kalebwbishop/smart-handicap-sign/frontend/pnpm-lock.yaml

lockfileVersion: '9.0'

settings:
  autoInstallPeers: true
  excludeLinksFromLockfile: false

importers:

  .:
    devDependencies:
      turbo:
        specifier: ^2.1.3
        version: 2.9.16
      typescript:
        specifier: ^5.6.3
        version: 5.9.3

  apps/mobile:
    dependencies:
      '@expo-google-fonts/jetbrains-mono':
        specifier: ^0.4.1
        version: 0.4.1
      '@expo-google-fonts/montserrat':
        specifier: ^0.4.2
        version: 0.4.2
      '@expo-google-fonts/outfit':
        specifier: ^0.4.3
        version: 0.4.3
      '@expo/metro-runtime':
        specifier: ~6.1.2
        version: 6.1.2(expo@54.0.35)(react-dom@19.1.0(react@19.1.0))(react-native@0.81.5(@babel/core@7.29.7)(@react-native/metro-config@0.85.3(@babel/core@7.29.7))(@types/react@19.1.17)(react@19.1.0))(react@19.1.0)
      '@expo/vector-icons':
        specifier: ^15.0.3
        version: 15.1.1(expo-font@14.0.12)(react-native@0.81.5(@babel/core@7.29.7)(@react-native/metro-config@0.85.3(@babel/core@7.29.7))(@types/react@19.1.17)(react@19.1.0))(react@19.1.0)
      '@hazard-hero/shared':
        specifier: workspace:*
        version: link:../../packages/shared
      '@react-native-async-storage/async-storage':
        specifier: 2.2.0
        version: 2.2.0(react-native@0.81.5(@babel/core@7.29.7)(@react-native/metro-config@0.85.3(@babel/core@7.29.7))(@types/react@19.1.17)(react@19.1.0))
      '@react-navigation/native':
        specifier: ^6.1.9
        version: 6.1.18(react-native@0.81.5(@babel/core@7.29.7)(@react-native/metro-config@0.85.3(@babel/core@7.29.7))(@types/react@19.1.17)(react@19.1.0))(react@19.1.0)
      '@react-navigation/native-stack':
        specifier: ^6.9.17
        version: 6.11.0(@react-navigation/native@6.1.18(react-native@0.81.5(@babel/core@7.29.7)(@react-native/metro-config@0.85.3(@babel/core@7.29.7))(@types/react@19.1.17)(react@19.1.0))(react@19.1.0))(react-native-safe-area-context@5.6.2(react-native@0.81.5(@babel/core@7.29.7)(@react-native/metro-config@0.85.3(@babel/core@7.29.7))(@types/react@19.1.17)(react@19.1.0))(react@19.1.0))(react-native-screens@4.16.0(react-native@0.81.5(@babel/core@7.29.7)(@react-native/metro-config@0.85.3(@babel/core@7.29.7))(@types/react@19.1.17)(react@19.1.0))(react@19.1.0))(react-native@0.81.5(@babel/core@7.29.7)(@react-native/metro-config@0.85.3(@babel/core@7.29.7))(@types/react@19.1.17)(react@19.1.0))(react@19.1.0)
      '@tanstack/react-query':
        specifier: ^5.17.9
        version: 5.101.0(react@19.1.0)
      axios:
        specifier: ^1.9.0
        version: 1.17.0
      deploy-box-react-native:
        specifier: file:../../../../deploy-box-react-native
        version: file:../../deploy-box-react-native(axios@1.17.0)(expo-linking@8.0.12)(expo-router@56.2.9)(expo-secure-store@15.0.8(expo@54.0.35))(expo-web-browser@55.0.16(expo@54.0.35)(react-native@0.81.5(@babel/core@7.29.7)(@react-native/metro-config@0.85.3(@babel/core@7.29.7))(@types/react@19.1.17)(react@19.1.0)))(react-native@0.81.5(@babel/core@7.29.7)(@react-native/metro-config@0.85.3(@babel/core@7.29.7))(@types/react@19.1.17)(react@19.1.0))(react@19.1.0)(zustand@4.5.7(@types/react@19.1.17)(react@19.1.0))
      expo:
        specifier: ~54.0.32
        version: 54.0.35(@babel/core@7.29.7)(@expo/dom-webview@56.0.5)(@expo/metro-runtime@6.1.2)(expo-router@56.2.9)(react-native@0.81.5(@babel/core@7.29.7)(@react-native/metro-config@0.85.3(@babel/core@7.29.7))(@types/react@19.1.17)(react@19.1.0))(react@19.1.0)(typescript@5.9.3)
      expo-av:
        specifier: ~16.0.8
        version: 16.0.8(expo@54.0.35)(react-native-web@0.21.2(react-dom@19.1.0(react@19.1.0))(react@19.1.0))(react-native@0.81.5(@babel/core@7.29.7)(@react-native/metro-config@0.85.3(@babel/core@7.29.7))(@types/react@19.1.17)(react@19.1.0))(react@19.1.0)
      expo-constants:
        specifier: ~18.0.10
        version: 18.0.13(expo@54.0.35)(react-native@0.81.5(@babel/core@7.29.7)(@react-native/metro-config@0.85.3(@babel/core@7.29.7))(@types/react@19.1.17)(react@19.1.0))
      expo-crypto:
        specifier: ~15.0.2
        version: 15.0.9(expo@54.0.35)
      expo-device:
        specifier: ~8.0.9
        version: 8.0.10(expo@54.0.35)
      expo-font:
        specifier: ~14.0.10
        version: 14.0.12(expo@54.0.35)(react-native@0.81.5(@babel/core@7.29.7)(@react-native/metro-config@0.85.3(@babel/core@7.29.7))(@types/react@19.1.17)(react@19.1.0))(react@19.1.0)
      expo-linking:
        specifier: ~8.0.11
        version: 8.0.12(expo@54.0.35)(react-native@0.81.5(@babel/core@7.29.7)(@react-native/metro-config@0.85.3(@babel/core@7.29.7))(@types/react@19.1.17)(react@19.1.0))(react@19.1.0)
      expo-notifications:
        specifier: ~0.32.12
        version: 0.32.17(expo@54.0.35)(react-native@0.81.5(@babel/core@7.29.7)(@react-native/metro-config@0.85.3(@babel/core@7.29.7))(@types/react@19.1.17)(react@19.1.0))(react@19.1.0)(typescript@5.9.3)
      expo-secure-store:
        specifier: ~15.0.8
        version: 15.0.8(expo@54.0.35)
      expo-status-bar:
        specifier: ~3.0.9
        version: 3.0.9(react-native@0.81.5(@babel/core@7.29.7)(@react-native/metro-config@0.85.3(@babel/core@7.29.7))(@types/react@19.1.17)(react@19.1.0))(react@19.1.0)
      expo-web-browser:
        specifier: ^55.0.9
        version: 55.0.16(expo@54.0.35)(react-native@0.81.5(@babel/core@7.29.7)(@react-native/metro-config@0.85.3(@babel/core@7.29.7))(@types/react@19.1.17)(react@19.1.0))
      linking:
        specifier: ^0.1.0-beta.5
        version: 0.1.0-beta.5
      react:
        specifier: 19.1.0
        version: 19.1.0
      react-dom:
        specifier: 19.1.0
        version: 19.1.0(react@19.1.0)
      react-native:
        specifier: 0.81.5
        version: 0.81.5(@babel/core@7.29.7)(@react-native/metro-config@0.85.3(@babel/core@7.29.7))(@types/react@19.1.17)(react@19.1.0)
      react-native-safe-area-context:
        specifier: ~5.6.0
        version: 5.6.2(react-native@0.81.5(@babel/core@7.29.7)(@react-native/metro-config@0.85.3(@babel/core@7.29.7))(@types/react@19.1.17)(react@19.1.0))(react@19.1.0)
      react-native-screens:
        specifier: ~4.16.0
        version: 4.16.0(react-native@0.81.5(@babel/core@7.29.7)(@react-native/metro-config@0.85.3(@babel/core@7.29.7))(@types/react@19.1.17)(react@19.1.0))(react@19.1.0)
      react-native-sse:
        specifier: ^1.2.1
        version: 1.2.1
      react-native-svg:
        specifier: ^15.15.5
        version: 15.15.5(react-native@0.81.5(@babel/core@7.29.7)(@react-native/metro-config@0.85.3(@babel/core@7.29.7))(@types/react@19.1.17)(react@19.1.0))(react@19.1.0)
      react-native-web:
        specifier: ^0.21.0
        version: 0.21.2(react-dom@19.1.0(react@19.1.0))(react@19.1.0)
      react-secure-storage:
        specifier: ^1.3.2
        version: 1.3.2
      zustand:
        specifier: ^4.4.7
        version: 4.5.7(@types/react@19.1.17)(react@19.1.0)
    devDependencies:
      '@babel/core':
        specifier: ^7.23.7
        version: 7.29.7
      '@playwright/test':
        specifier: ^1.59.1
        version: 1.60.0
      '@testing-library/react-native':
        specifier: ^12.4.3
        version: 12.9.0(jest@29.7.0(@types/node@22.19.20))(react-native@0.81.5(@babel/core@7.29.7)(@react-native/metro-config@0.85.3(@babel/core@7.29.7))(@types/react@19.1.17)(react@19.1.0))(react-test-renderer@19.1.0(react@19.1.0))(react@19.1.0)
      '@types/react':
        specifier: ~19.1.10
        version: 19.1.17
      '@types/react-native':
        specifier: ~0.73.0
        version: 0.73.0(@babel/core@7.29.7)(@react-native/metro-config@0.85.3(@babel/core@7.29.7))(@types/react@19.1.17)(react@19.1.0)
      '@types/react-navigation':
        specifier: ^3.0.8
        version: 3.4.0
      '@typescript-eslint/eslint-plugin':
        specifier: ^8.60.0
        version: 8.60.1(@typescript-eslint/parser@8.60.1(eslint@8.57.1)(typescript@5.9.3))(eslint@8.57.1)(typescript@5.9.3)
      '@typescript-eslint/parser':
        specifier: ^8.60.0
        version: 8.60.1(eslint@8.57.1)(typescript@5.9.3)
      eslint:
        specifier: ^8.56.0
        version: 8.57.1
      eslint-config-expo:
        specifier: ~10.0.0
        version: 10.0.0(eslint@8.57.1)(typescript@5.9.3)
      jest:
        specifier: ^29.7.0
        version: 29.7.0(@types/node@22.19.20)
      playwright:
        specifier: ^1.59.1
        version: 1.60.0
      react-native-dotenv:
        specifier: ^3.4.11
        version: 3.4.11(@babel/runtime@7.29.7)
      react-test-renderer:
        specifier: 19.1.0
        version: 19.1.0(react@19.1.0)
      typescript:
        specifier: ^5.3.3
        version: 5.9.3

  apps/web:
    dependencies:
      '@hazard-hero/shared':
        specifier: workspace:*
        version: link:../../packages/shared
      axios:
        specifier: ^1.9.0
        version: 1.17.0
      next:
        specifier: ^15.4.0
        version: 15.5.19(@playwright/test@1.60.0)(babel-plugin-react-compiler@1.0.0)(react-dom@19.1.0(react@19.1.0))(react@19.1.0)
      react:
        specifier: 19.1.0
        version: 19.1.0
      react-dom:
        specifier: 19.1.0
        version: 19.1.0(react@19.1.0)
    devDependencies:
      '@types/node':
        specifier: ^22.10.2
        version: 22.19.20
      '@types/react':
        specifier: ^19.1.10
        version: 19.1.17
      '@types/react-dom':
        specifier: ^19.1.9
        version: 19.2.3(@types/react@19.1.17)
      typescript:
        specifier: ^5.6.3
        version: 5.9.3

  packages/eslint-config: {}

  packages/shared:
    devDependencies:
      typescript:
        specifier: ^5.6.3
        version: 5.9.3

  packages/tsconfig: {}

  packages/ui:
    devDependencies:
      typescript:
        specifier: ^5.6.3
        version: 5.9.3

packages:

  '@0no-co/graphql.web@1.2.0':
    resolution: {integrity: sha512-/1iHy9TTr63gE1YcR5idjx8UREz1s0kFhydf3bBLCXyqjhkIc6igAzTOx3zPifCwFR87tsh/4Pa9cNts6d2otw==}
    peerDependencies:
      graphql: ^14.0.0 || ^15.0.0 || ^16.0.0
    peerDependenciesMeta:
      graphql:
        optional: true

  '@adobe/css-tools@4.5.0':
    resolution: {integrity: sha512-6OzddxPio9UiWTCemp4N8cYLV2ZN1ncRnV1cVGtve7dhPOtRkleRyx32GQCYSwDYgaHU3USMm84tNsvKzRCa1Q==}

  '@babel/code-frame@7.10.4':
    resolution: {integrity: sha512-vG6SvB6oYEhvgisZNFRmRCUkLz11c7rp+tbNTynGqc6mS1d5ATd/sGyV6W0KZZnXRKMTzZDRgQT3Ou9jhpAfUg==}

  '@babel/code-frame@7.29.7':
    resolution: {integrity: sha512-Aup7aUOfpbAUg2ROOJN6Iw5f9DMBlzu0mIkm/malLQFN/YQgO48wCj0Kxa3sEHJvPVFg7siR+qRInwXd2qhQKw==}
    engines: {node: '>=6.9.0'}

  '@babel/compat-data@7.29.7':
    resolution: {integrity: sha512-locTkQyKvwIEgBzVrn8693ebc97F2U8ZHjbXwDXJ5Fn2TCpNwTlKcaKLkdHop5c/icOFE7qt7Q9JC5hnKNa6Gg==}
    engines: {node: '>=6.9.0'}

  '@babel/core@7.29.7':
    resolution: {integrity: sha512-RgHBCvtjbOK2gXSNBNIkNoEc9qoVEtau3hj8gEqKQuL3HZAibKarWFEI3Lfm6EYKkLalOh8eSrj9b+ch9H/VBA==}
    engines: {node: '>=6.9.0'}

  '@babel/generator@7.29.7':
    resolution: {integrity: sha512-DkXD5OJQaAQIdZ1bt3UZdEnHAn9Imd3IVBdX03UFe+ony9Ojw5pzr9YVKGDY1jt+Gcn/FnGkNf8r+Vj5NOJWtQ==}
    engines: {node: '>=6.9.0'}

  '@babel/helper-annotate-as-pure@7.29.7':
    resolution: {integrity: sha512-OoK6239jHPuSQOoS0kfTVKn0b/rVTk0seKq4Gd2UMLtmOVLjDC0ki3e+c90Trqv2gMfvJFqkiljrr568+qddiw==}
    engines: {node: '>=6.9.0'}

  '@babel/helper-compilation-targets@7.29.7':
    resolution: {integrity: sha512-wem6WaBj4NaVYVdNhLPPVacES6ZJ+KBBfSkTMD3YZxbP3rm3Di85tJU5ljaUNhaOynt+Aj0xruhYuzQBt8n71g==}
    engines: {node: '>=6.9.0'}

  '@babel/helper-create-class-features-plugin@7.29.7':
    resolution: {integrity: sha512-IY3ZD9Tmooqr3TUhc3DUWxiuo8xx1DWLhd5M7hQ+ZWJamqM2BbalrBJb2MisSLoYorOj75U03qULCxQTY9r3hg==}
    engines: {node: '>=6.9.0'}
    peerDependencies:
      '@babel/core': ^7.0.0

  '@babel/helper-create-regexp-features-plugin@7.29.7':
    resolution: {integrity: sha512-907Uymvqgg1dwUA+7IGwFAOSYzQOuzPXKNJ1yxzwPffzkYFg2q2eHi1fIOs6sXkG9NbIUMunnUlkYsfRFNvomg==}
    engines: {node: '>=6.9.0'}
    peerDependencies:
      '@babel/core': ^7.0.0

  '@babel/helper-define-polyfill-provider@0.6.8':
    resolution: {integrity: sha512-47UwBLPpQi1NoWzLuHNjRoHlYXMwIJoBf7MFou6viC/sIHWYygpvr0B6IAyh5sBdA2nr2LPIRww8lfaUVQINBA==}
    peerDependencies:
      '@babel/core': ^7.4.0 || ^8.0.0-0 <8.0.0

  '@babel/helper-globals@7.29.7':
    resolution: {integrity: sha512-3nQVUAtvkKH9zahfWgw96Jc/uFOmjACE1kQz82E2lqWmHBgjzbNlsC22nuQTfahmWeQtTq5nQ/4Nnd2A1wj4zA==}
    engines: {node: '>=6.9.0'}

  '@babel/helper-member-expression-to-functions@7.29.7':
    resolution: {integrity: sha512-j+7JYmk1JYDtACIGj0QJqqWZjoUpMoEikQGADMaHgCMCSDqd2+P32rfcibUNrGOMWrlzK1WJBdxrB3JJQZwWtg==}
    engines: {node: '>=6.9.0'}

  '@babel/helper-module-imports@7.29.7':
    resolution: {integrity: sha512-ejHwrQQYcm9xnTivShn2IDOlIzInN34AXskvq9QicvCtEzq1Vzclu/tKF8Jq1Cg8JG2GL6/EmjgsCT7lXepE3g==}
    engines: {node: '>=6.9.0'}

  '@babel/helper-module-transforms@7.29.7':
    resolution: {integrity: sha512-UPUVSyXbOh627KiCIGQSgwWzGeBKLkaJ9PJEdrngIwMSzxLR4jS4+f1f1jb7VzBbg8nFLaYotvVPFCTqdrmTAg==}
    engines: {node: '>=6.9.0'}
    peerDependencies:
      '@babel/core': ^7.0.0

  '@babel/helper-optimise-call-expression@7.29.7':
    resolution: {integrity: sha512-+kmGVjcT9RGYzoDwdwEqEvGgKe3BYq+O1iGzjFubaNgZHwYHP6lsF2Yghf4kEuv9BV7tYDZ913aBW9am6YKong==}
    engines: {node: '>=6.9.0'}

  '@babel/helper-plugin-utils@7.29.7':
    resolution: {integrity: sha512-G7sHYigPY17oO5SYWnfD/0MTBwVR781S/JI643e/JhUYgVgWE/61SoW3NH9KWUKyKq5LVh3npif99Wkt6j86Jw==}
    engines: {node: '>=6.9.0'}

  '@babel/helper-remap-async-to-generator@7.29.7':
    resolution: {integrity: sha512-16AMiW26DbXWBbr3B8wNozKM0ydMLB892vaOaJW/fPJdnT8vJk5sdkQcU/isqUxyCE0cEoa8wZOcbgDuC4b6Og==}
    engines: {node: '>=6.9.0'}
    peerDependencies:
      '@babel/core': ^7.0.0

  '@babel/helper-replace-supers@7.29.7':
    resolution: {integrity: sha512-atfGXWSeCiF4DnKZIfmJfQRkSw9b9gNNXR1kqKjbhG4pGYCOnkp8OcTB8E3NXjBu8NpheSnOeNKz8KT7UNFTmQ==}
    engines: {node: '>=6.9.0'}
    peerDependencies:
      '@babel/core': ^7.0.0

  '@babel/helper-skip-transparent-expression-wrappers@7.29.7':
    resolution: {integrity: sha512-brcMGQaVzIeUb+6/bs1Av0f8YuNNjKY2JyvfRCsFuFsdKccEQ5Ges2y74D74NZ1Rz8lKJ9ksJkfqwQFJ/iNEyQ==}
    engines: {node: '>=6.9.0'}

  '@babel/helper-string-parser@7.29.7':
    resolution: {integrity: sha512-Pb5ijPrZ89GDH8223L4UP8i6QApWxs04RbPQJTeWDV0/keR2E36MeKnyr6LYmUUvqRRI+Iv87SuF1W6ErINzYw==}
    engines: {node: '>=6.9.0'}

  '@babel/helper-validator-identifier@7.29.7':
    resolution: {integrity: sha512-qehxGkRj55h/ff8EMaJ+cYhyaKlHIxqYDn682wQD7RNp9UujOQsHog2uS0r2vzr4pW+sXf90NeeayjcNaX3fFg==}
    engines: {node: '>=6.9.0'}

  '@babel/helper-validator-option@7.29.7':
    resolution: {integrity: sha512-N9ZErrD+yW5geCDtBqnOoxmR8+tNKiGuxKlDpuJxfsqpa2dFcexaziGAE/qoHLiDDreVNMupxGmSoNlyvsA3gw==}
    engines: {node: '>=6.9.0'}

  '@babel/helper-wrap-function@7.29.7':
    resolution: {integrity: sha512-iES0Skag9ERIF68aXadpO6dbXa03mNWK3sEqJaMnLNs/eC3l0lkImdfoy6Y09/SfkpawdAB4RjQ7PVA7TcVGdw==}
    engines: {node: '>=6.9.0'}

  '@babel/helpers@7.29.7':
    resolution: {integrity: sha512-1k2lAGRMfHTcwuNYcCNUmaUffmQv8KWMfh2iJUUeRlwlwH4FdNG7mfPI10NPfLHJFThE4Tyr4mv7kTNZOiPuBg==}
    engines: {node: '>=6.9.0'}

  '@babel/highlight@7.25.9':
    resolution: {integrity: sha512-llL88JShoCsth8fF8R4SJnIn+WLvR6ccFxu1H3FlMhDontdcmZWf2HgIZ7AIqV3Xcck1idlohrN4EUBQz6klbw==}
    engines: {node: '>=6.9.0'}

  '@babel/parser@7.29.7':
    resolution: {integrity: sha512-hnORnjP/1P/zFEndoeX+n+t1RwWRJiJpM/jO7FW32Kn9r5+sJB2JWOdYo4L6k78j15eCwY3Gm/7364B1EMwtNg==}
    engines: {node: '>=6.0.0'}
    hasBin: true

  '@babel/plugin-proposal-decorators@7.29.7':
    resolution: {integrity: sha512-EtU0Hi3GvrTqD56xKmZvV/uCXK2ZbwVNPNLAquVItcAZpUhkXwWlo3Fmj0c2LxgSf2I8IDULeAepwNP1OefLXg==}
    engines: {node: '>=6.9.0'}
    peerDependencies:
      '@babel/core': ^7.0.0-0

  '@babel/plugin-proposal-export-default-from@7.29.7':
    resolution: {integrity: sha512-p+G5BNXDcy3bOXplhY4HybQ1GxH3i2Tppmdm/3epyRu2VgJJZuUlZ61MqRTg582Q7ZLBdP7fePYvsumSEkMxcQ==}
    engines: {node: '>=6.9.0'}
    peerDependencies:
      '@babel/core': ^7.0.0-0

  '@babel/plugin-syntax-async-generators@7.8.4':
    resolution: {integrity: sha512-tycmZxkGfZaxhMRbXlPXuVFpdWlXpir2W4AMhSJgRKzk/eDlIXOhb2LHWoLpDF7TEHylV5zNhykX6KAgHJmTNw==}
    peerDependencies:
      '@babel/core': ^7.0.0-0

  '@babel/plugin-syntax-bigint@7.8.3':
    resolution: {integrity: sha512-wnTnFlG+YxQm3vDxpGE57Pj0srRU4sHE/mDkt1qv2YJJSeUAec2ma4WLUnUPeKjyrfntVwe/N6dCXpU+zL3Npg==}
    peerDependencies:
      '@babel/core': ^7.0.0-0

  '@babel/plugin-syntax-class-properties@7.12.13':
    resolution: {integrity: sha512-fm4idjKla0YahUNgFNLCB0qySdsoPiZP3iQE3rky0mBUtMZ23yDJ9SJdg6dXTSDnulOVqiF3Hgr9nbXvXTQZYA==}
    peerDependencies:
      '@babel/core': ^7.0.0-0

  '@babel/plugin-syntax-class-static-block@7.14.5':
    resolution: {integrity: sha512-b+YyPmr6ldyNnM6sqYeMWE+bgJcJpO6yS4QD7ymxgH34GBPNDM/THBh8iunyvKIZztiwLH4CJZ0RxTk9emgpjw==}
    engines: {node: '>=6.9.0'}
    peerDependencies:
      '@babel/core': ^7.0.0-0

  '@babel/plugin-syntax-decorators@7.29.7':
    resolution: {integrity: sha512-9MTTLbF39X6sqM92JPEsoI7++26hjZvzkxKZy64aMhWLH2mPkJ/Q3AV4QLmls3R14FpSpkOwQQfUh962JGQxxg==}
    engines: {node: '>=6.9.0'}
    peerDependencies:
      '@babel/core': ^7.0.0-0

  '@babel/plugin-syntax-dynamic-import@7.8.3':
    resolution: {integrity: sha512-5gdGbFon+PszYzqs83S3E5mpi7/y/8M9eC90MRTZfduQOYW76ig6SOSPNe41IG5LoP3FGBn2N0RjVDSQiS94kQ==}
    peerDependencies:
      '@babel/core': ^7.0.0-0

  '@babel/plugin-syntax-export-default-from@7.29.7':
    resolution: {integrity: sha512-foag0BB37ROhdeIX9O8G0jX7hw0UekJc04cHMrYLOnrErsnBKqJGHJ8eDRpoCFZBvEPPygmmtw4qyU97qa4oOw==}
    engines: {node: '>=6.9.0'}
    peerDependencies:
      '@babel/core': ^7.0.0-0

  '@babel/plugin-syntax-flow@7.29.7':
    resolution: {integrity: sha512-ajMX6QPcyomotqwpzhkYGxcK2i/us0rs1Qo9QvUpa+Fca0FTmqrzKrctoIYLMxcOhGZldGT/BAVkRGTWBiR8gQ==}
    engines: {node: '>=6.9.0'}
    peerDependencies:
      '@babel/core': ^7.0.0-0

  '@babel/plugin-syntax-import-attributes@7.29.7':
    resolution: {integrity: sha512-zGYcYfq/WmZ4V+kBIXQon9dSSc8ircGZqw9ZaNhhGj9nZkeBu1jHLBDQqYYi5WA9uawvA2sIMbry2nCFhf5Djg==}
    engines: {node: '>=6.9.0'}
    peerDependencies:
      '@babel/core': ^7.0.0-0

  '@babel/plugin-syntax-import-meta@7.10.4':
    resolution: {integrity: sha512-Yqfm+XDx0+Prh3VSeEQCPU81yC+JWZ2pDPFSS4ZdpfZhp4MkFMaDC1UqseovEKwSUpnIL7+vK+Clp7bfh0iD7g==}
    peerDependencies:
      '@babel/core': ^7.0.0-0

  '@babel/plugin-syntax-json-strings@7.8.3':
    resolution: {integrity: sha512-lY6kdGpWHvjoe2vk4WrAapEuBR69EMxZl+RoGRhrFGNYVK8mOPAW8VfbT/ZgrFbXlDNiiaxQnAtgVCZ6jv30EA==}
    peerDependencies:
      '@babel/core': ^7.0.0-0

  '@babel/plugin-syntax-jsx@7.29.7':
    resolution: {integrity: sha512-TSu8+mHCoEaaCDEZ0I3+6mvTBYR4PCxQwf2z9/r5Tbztv6NaLR3B9thGTTxX2WGuGHJqRiAbKPeGTJ5XWXVg6A==}
    engines: {node: '>=6.9.0'}
    peerDependencies:
      '@babel/core': ^7.0.0-0

  '@babel/plugin-syntax-logical-assignment-operators@7.10.4':
    resolution: {integrity: sha512-d8waShlpFDinQ5MtvGU9xDAOzKH47+FFoney2baFIoMr952hKOLp1HR7VszoZvOsV/4+RRszNY7D17ba0te0ig==}
    peerDependencies:
      '@babel/core': ^7.0.0-0

  '@babel/plugin-syntax-nullish-coalescing-operator@7.8.3':
    resolution: {integrity: sha512-aSff4zPII1u2QD7y+F8oDsz19ew4IGEJg9SVW+bqwpwtfFleiQDMdzA/R+UlWDzfnHFCxxleFT0PMIrR36XLNQ==}
    peerDependencies:
      '@babel/core': ^7.0.0-0

  '@babel/plugin-syntax-numeric-separator@7.10.4':
    resolution: {integrity: sha512-9H6YdfkcK/uOnY/K7/aA2xpzaAgkQn37yzWUMRK7OaPOqOpGS1+n0H5hxT9AUw9EsSjPW8SVyMJwYRtWs3X3ug==}
    peerDependencies:
      '@babel/core': ^7.0.0-0

  '@babel/plugin-syntax-object-rest-spread@7.8.3':
    resolution: {integrity: sha512-XoqMijGZb9y3y2XskN+P1wUGiVwWZ5JmoDRwx5+3GmEplNyVM2s2Dg8ILFQm8rWM48orGy5YpI5Bl8U1y7ydlA==}
    peerDependencies:
      '@babel/core': ^7.0.0-0

  '@babel/plugin-syntax-optional-catch-binding@7.8.3':
    resolution: {integrity: sha512-6VPD0Pc1lpTqw0aKoeRTMiB+kWhAoT24PA+ksWSBrFtl5SIRVpZlwN3NNPQjehA2E/91FV3RjLWoVTglWcSV3Q==}
    peerDependencies:
      '@babel/core': ^7.0.0-0

  '@babel/plugin-syntax-optional-chaining@7.8.3':
    resolution: {integrity: sha512-KoK9ErH1MBlCPxV0VANkXW2/dw4vlbGDrFgz8bmUsBGYkFRcbRwMh6cIJubdPrkxRwuGdtCk0v/wPTKbQgBjkg==}
    peerDependencies:
      '@babel/core': ^7.0.0-0

  '@babel/plugin-syntax-private-property-in-object@7.14.5':
    resolution: {integrity: sha512-0wVnp9dxJ72ZUJDV27ZfbSj6iHLoytYZmh3rFcxNnvsJF3ktkzLDZPy/mA17HGsaQT3/DQsWYX1f1QGWkCoVUg==}
    engines: {node: '>=6.9.0'}
    peerDependencies:
      '@babel/core': ^7.0.0-0

  '@babel/plugin-syntax-top-level-await@7.14.5':
    resolution: {integrity: sha512-hx++upLv5U1rgYfwe1xBQUhRmU41NEvpUvrp8jkrSCdvGSnM5/qdRMtylJ6PG5OFkBaHkbTAKTnd3/YyESRHFw==}
    engines: {node: '>=6.9.0'}
    peerDependencies:
      '@babel/core': ^7.0.0-0

  '@babel/plugin-syntax-typescript@7.29.7':
    resolution: {integrity: sha512-ngr+82Sh0xMz25TPCZi+nC2iTzjfCdWS2ONXTp/PtSCHCgaCNBpdMqgvJ2ccdLlClVZ7sisIgB914j/JFe+RZA==}
    engines: {node: '>=6.9.0'}
    peerDependencies:
      '@babel/core': ^7.0.0-0

  '@babel/plugin-transform-arrow-functions@7.29.7':
    resolution: {integrity: sha512-N7zArUXWzAMzm+/N0uPBeVB3Fam5lMxtUwMmDK5f/IBBS7a7p1qeUoxd/6CckXoxUdgsntq1Dh8xNW06maZbDQ==}
    engines: {node: '>=6.9.0'}
    peerDependencies:
      '@babel/core': ^7.0.0-0

  '@babel/plugin-transform-async-generator-functions@7.29.7':
    resolution: {integrity: sha512-d98gXZkgswvkyohMBABkhm3GeXhYj8psWfwQ2C7gtfrKGTykQa/iOIi+JJhwMjPlZ6Vm2XN+DCf3Es1EoG4ZLA==}
    engines: {node: '>=6.9.0'}
    peerDependencies:
      '@babel/core': ^7.0.0-0

  '@babel/plugin-transform-async-to-generator@7.29.7':
    resolution: {integrity: sha512-pcUb2SS+RMo9TWVBwKGI5ShtoG7R+zBsFmCKDa6fe8c+hPr3XJlZgoE5j6i8W7gDjhyvy+85vmYexanvXh3d1w==}
    engines: {node: '>=6.9.0'}
    peerDependencies:
      '@babel/core': ^7.0.0-0

  '@babel/plugin-transform-block-scoping@7.29.7':
    resolution: {integrity: sha512-ONyr4+AZhKh8yKWInVxU9AXA9EbsyeLcL6V0dJy6M2/62vuvpGm29zzuymbTpdc451GEpDIdAyPLP3r+P61yKQ==}
    engines: {node: '>=6.9.0'}
    peerDependencies:
      '@babel/core': ^7.0.0-0

  '@babel/plugin-transform-class-properties@7.29.7':
    resolution: {integrity: sha512-GtcpjFvanPfzNQi3eTitsCqtRRmmqzpy/A+yhTR1HaZo1Ly3EA8ZXxlPyHdR8/IuRMYc3E4wdGBewB2QKQjAaA==}
    engines: {node: '>=6.9.0'}
    peerDependencies:
      '@babel/core': ^7.0.0-0

  '@babel/plugin-transform-class-static-block@7.29.7':
    resolution: {integrity: sha512-kibJgmEdX2iMwsHY2tSZNDgj8PwIlCQz7FK9KuGKO8zsuoUwSEhoNnNVp/emKWrbY4HeO6kkXfdMqRKKKXBm2A==}
    engines: {node: '>=6.9.0'}
    peerDependencies:
      '@babel/core': ^7.12.0

  '@babel/plugin-transform-classes@7.29.7':
    resolution: {integrity: sha512-qV0OGGBVacduzQHE649JyCneOFI/maT+YKsO+K4Yi3xv2wTPNjM/W2o2gdzMwEAZz7fXNTHAe0NcSg30bIN69g==}
    engines: {node: '>=6.9.0'}
    peerDependencies:
      '@babel/core': ^7.0.0-0

  '@babel/plugin-transform-computed-properties@7.29.7':
    resolution: {integrity: sha512-RK7/IyU5phpuCdBAuig5VkzG/EnbDaui5SQGdU9BFrHdV+mV4cUjLMQ9lJDjLNtWHsqtiefpGZUXQP2BiTYMsA==}
    engines: {node: '>=6.9.0'}
    peerDependencies:
      '@babel/core': ^7.0.0-0

  '@babel/plugin-transform-destructuring@7.29.7':
    resolution: {integrity: sha512-iPX8aD6H9zV5s7ZsqTdNocPN/MGQ5sSMnElKrktxjJRMnB2jN/1p2+R7GkfD6CAYoVFqy5A4XnSIUeGgJzIWpg==}
    engines: {node: '>=6.9.0'}
    peerDependencies:
      '@babel/core': ^7.0.0-0

  '@babel/plugin-transform-export-namespace-from@7.29.7':
    resolution: {integrity: sha512-24B2nOy2TeJSMheqwPD4DDQOV/elLSIlKxjZt4i05H5AgdPdWR3n18HnNrcJ+j76WJd9gbwb9jPjNYUy6RautA==}
    engines: {node: '>=6.9.0'}
    peerDependencies:
      '@babel/core': ^7.0.0-0

  '@babel/plugin-transform-flow-strip-types@7.29.7':
    resolution: {integrity: sha512-wRHeUjUjCZnMHmiO5bRgjFLcoEh7JyTdByOW11ahhwNa4V0bmeGEaIvt51yq0zQp2yWIpqfxXXPyUP6GFJZHOQ==}
    engines: {node: '>=6.9.0'}
    peerDependencies:
      '@babel/core': ^7.0.0-0

  '@babel/plugin-transform-for-of@7.29.7':
    resolution: {integrity: sha512-zeSIHh0+E1Um1WJRXCFlHQYu2ieJNdivLLjlBEp+dIBu3S51n+SZZmIXjxnItw6pz56Cn+KvK68BIBVsxq2JiQ==}
    engines: {node: '>=6.9.0'}
    peerDependencies:
      '@babel/core': ^7.0.0-0

  '@babel/plugin-transform-function-name@7.29.7':
    resolution: {integrity: sha512-otRWaHXE6fbAGkePvaj/kvs3HsqXfPhlnzwSOlnFgbqCPMd975dW+4wZ00WFBt+/YlBGcJwNrARQTOJOb4ZrIg==}
    engines: {node: '>=6.9.0'}
    peerDependencies:
      '@babel/core': ^7.0.0-0

  '@babel/plugin-transform-literals@7.29.7':
    resolution: {integrity: sha512-DZ/oLP21ZuWx1vKqnoNv6/tvEK48AQOBRai40CX9dTjGluvT/YZCyY3rryDtyUqCEoyNroy5KKPwX2iQCiRvyw==}
    engines: {node: '>=6.9.0'}
    peerDependencies:
      '@babel/core': ^7.0.0-0

  '@babel/plugin-transform-logical-assignment-operators@7.29.7':
    resolution: {integrity: sha512-A0H91hh6W8MFRkp5TqJmMr39jzGD1A1E1Ysiv2O06Sfbhkapm+XyIzxWCEh5kqwOZ1/8QZ0dY3SeQ7XBqfJd5Q==}
    engines: {node: '>=6.9.0'}
    peerDependencies:
      '@babel/core': ^7.0.0-0

  '@babel/plugin-transform-modules-commonjs@7.29.7':
    resolution: {integrity: sha512-j0vCldybPC5b5dwCQOJ21uKtHzt7hxLygJTg9eF1ScfaikEDNfzn94XoW5Fi+seBR0nCyL23xaBFFkq7dTM8XQ==}
    engines: {node: '>=6.9.0'}
    peerDependencies:
      '@babel/core': ^7.0.0-0

  '@babel/plugin-transform-named-capturing-groups-regex@7.29.7':
    resolution: {integrity: sha512-vuFoLwr4qnv2xbZ16SQd6uPcH5FNrLHhk/Jzo++0XJFcaDsr4gjJVg6j398oMHiC+83k/GiBzviwF5KBJkPUtQ==}
    engines: {node: '>=6.9.0'}
    peerDependencies:
      '@babel/core': ^7.0.0

  '@babel/plugin-transform-nullish-coalescing-operator@7.29.7':
    resolution: {integrity: sha512-idmp1dFaekP9GbcMvG24Kvw2BfhFZjHnNJCkV4WuIY4PskJzwI3f1N5OdgYke38T7rftO6ERulFRn2cFeZwRkg==}
    engines: {node: '>=6.9.0'}
    peerDependencies:
      '@babel/core': ^7.0.0-0

  '@babel/plugin-transform-numeric-separator@7.29.7':
    resolution: {integrity: sha512-zR7fv/z14OjgHl4AgRtkDBvBMhIzCxqV/qN/2BCRC7LjFwvuzjYe7gDWxC4Wl/SNsLM6SE1IWvRPYMgSJaUvNw==}
    engines: {node: '>=6.9.0'}
    peerDependencies:
      '@babel/core': ^7.0.0-0

  '@babel/plugin-transform-object-rest-spread@7.29.7':
    resolution: {integrity: sha512-Ld98jn4c0smUywL57m7SgsHq3OpThOa6LqZJif3G6jYOovPleoFhVrBJ1WegRApSFB2wu4+RelAj9AC9G08Z4A==}
    engines: {node: '>=6.9.0'}
    peerDependencies:
      '@babel/core': ^7.0.0-0

  '@babel/plugin-transform-optional-catch-binding@7.29.7':
    resolution: {integrity: sha512-sLsyndxK2VwX6yNUOakMb7Sh553ZTe/vVM1XJ+9Z5aW1ytsc8xOIwmyk05NNjN60vkc5/KqoTH6hB4V41LJhng==}
    engines: {node: '>=6.9.0'}
    peerDependencies:
      '@babel/core': ^7.0.0-0

  '@babel/plugin-transform-optional-chaining@7.29.7':
    resolution: {integrity: sha512-6GM1dhvK3gNODkXcEcMCOLEDCLSoZ/sBbro2Ax8HURyasQ4NshagQixkRFdh5niI6E4gmA/jYI/4aT7rRos3ZQ==}
    engines: {node: '>=6.9.0'}
    peerDependencies:
      '@babel/core': ^7.0.0-0

  '@babel/plugin-transform-parameters@7.29.7':
    resolution: {integrity: sha512-ZDOBqV/qLYJI0YElr8DcENEyARsFQeESqWXH6gZlghYXuPPjvweuDhP4VyEi4BlUBlLRFZVjxoZDMjxhLW766g==}
    engines: {node: '>=6.9.0'}
    peerDependencies:
      '@babel/core': ^7.0.0-0

  '@babel/plugin-transform-private-methods@7.29.7':
    resolution: {integrity: sha512-/6Rz4DK1ETDEM/bWHsPHcaEe7ZaT1EqSXjtSP/L0DijOYuaUhiRiOKcwpZ8P7zR4xXEHc2ITdiCgBm9Tpyv9ug==}
    engines: {node: '>=6.9.0'}
    peerDependencies:
      '@babel/core': ^7.0.0-0

  '@babel/plugin-transform-private-property-in-object@7.29.7':
    resolution: {integrity: sha512-+BNo06dnrzdNNqCm1X6YUaVv0DKk8Q+JYcoZfOkLhYWNCXzlwTSRq8zGWayT1csjcpNXV9CQTBRRbmTLZac5cA==}
    engines: {node: '>=6.9.0'}
    peerDependencies:
      '@babel/core': ^7.0.0-0

  '@babel/plugin-transform-react-display-name@7.29.7':
    resolution: {integrity: sha512-+1wdDMGNb4UPeY3Q4L5yLiYe6TXPXubs4NjrgRFw13hPRLJfEMw2Q5OXkee6/IfdqePIeW4Jjwe3aBh7SdKz4Q==}
    engines: {node: '>=6.9.0'}
    peerDependencies:
      '@babel/core': ^7.0.0-0

  '@babel/plugin-transform-react-jsx-development@7.29.7':
    resolution: {integrity: sha512-Xfy3UVMF04+ypnFbkhvfqtmvwfe92qwQdbGZVonhE+6v35GzlofmOnA1szaZqzb9xYWr0nl1e5EMmzi0DNON1g==}
    engines: {node: '>=6.9.0'}
    peerDependencies:
      '@babel/core': ^7.0.0-0

  '@babel/plugin-transform-react-jsx-self@7.29.7':
    resolution: {integrity: sha512-TL0hMc9xzy86VD31nUiwzd5otRAcyEPcsegCxolO0PvcXuH1v0kECe/UIznYFihpkvU5wg/jk4v0TTEFfm53fw==}
    engines: {node: '>=6.9.0'}
    peerDependencies:
      '@babel/core': ^7.0.0-0

  '@babel/plugin-transform-react-jsx-source@7.29.7':
    resolution: {integrity: sha512-06IyK09H3wi4cGbhDBwp5gUGo0IKtnYa8tyTiephirPCK6fbobVGiXMMI5zLQ4aKEYP3wZ3ArU44o+8KMrSG/Q==}
    engines: {node: '>=6.9.0'}
    peerDependencies:
      '@babel/core': ^7.0.0-0

  '@babel/plugin-transform-react-jsx@7.29.7':
    resolution: {integrity: sha512-WsZulLVBUHXVj2cUcPVx6UE21TpalB6bHbSFErKT0Ib++ax24jjXe73FqlWvdylFOjiuPHYi6VCcgRad1ItN+A==}
    engines: {node: '>=6.9.0'}
    peerDependencies:
      '@babel/core': ^7.0.0-0

  '@babel/plugin-transform-react-pure-annotations@7.29.7':
    resolution: {integrity: sha512-H5E+HBgDpr6Q5t+Aj11tL7XkIui1jhbIoArVQnqjgXo5/3YxkN7ZEBcWF4RQlB0T4rrxJQbXS6kiFV6B7XTqUA==}
    engines: {node: '>=6.9.0'}
    peerDependencies:
      '@babel/core': ^7.0.0-0

  '@babel/plugin-transform-regenerator@7.29.7':
    resolution: {integrity: sha512-rNNFV0DBAJp988xW2DOntfDoYn1eR8GGF5AT5vYc+rjyfaQkM242c9tZUHHPe7KYaiJizXPWhQTzzdbXySyhBw==}
    engines: {node: '>=6.9.0'}
    peerDependencies:
      '@babel/core': ^7.0.0-0

  '@babel/plugin-transform-runtime@7.29.7':
    resolution: {integrity: sha512-xmAscdE/AsqRW7vutbPNoUmu/nF5SrLKPs7aoJgEjo35lLKA/Bc0i2rMv/hr1+Y0o1bQCiVtith3u2vdgRL39Q==}
    engines: {node: '>=6.9.0'}
    peerDependencies:
      '@babel/core': ^7.0.0-0

  '@babel/plugin-transform-shorthand-properties@7.29.7':
    resolution: {integrity: sha512-I+WYbGBAiCn7nA6xBrlgPH+MB7HWb4u8pv5S0Pv7OtwNvIFvCCb24YlttKEeUFVurfBCEaOTnuhlqsb7f0Z5Dg==}
    engines: {node: '>=6.9.0'}
    peerDependencies:
      '@babel/core': ^7.0.0-0

  '@babel/plugin-transform-spread@7.29.7':
    resolution: {integrity: sha512-/u5K1QWada7tbYNqTjMh96718g9NTwh9tfPJMsSmVsQwGT447FskV+KcfeXkXq2GWki4EM/MuTdmBec+hOuVTQ==}
    engines: {node: '>=6.9.0'}
    peerDependencies:
      '@babel/core': ^7.0.0-0

  '@babel/plugin-transform-sticky-regex@7.29.7':
    resolution: {integrity: sha512-BCHzNYJGe9l7EpwwDBN/ztlL2NYFFq8hp9ddjtUEM9f2O7S7kKV/lL6Fwo7IF7NSkYhPK2vO+86nIGltA90MsA==}
    engines: {node: '>=6.9.0'}
    peerDependencies:
      '@babel/core': ^7.0.0-0

  '@babel/plugin-transform-template-literals@7.29.7':
    resolution: {integrity: sha512-NCSEJ4sLFU2gqAub45HYh4fus2yQ36rr6ei6vpU7NdoJqCpxvEG8E6eJpscGyXP3VHD2Ny+fSXr04k1hoUrFqA==}
    engines: {node: '>=6.9.0'}
    peerDependencies:
      '@babel/core': ^7.0.0-0

  '@babel/plugin-transform-typescript@7.29.7':
    resolution: {integrity: sha512-jK52h8LaLc7JarhQV2ofeFMts4H7vnOXnqZNA6fYglBTZewRBE51KWt3BUltW1P+KoPsYkHoJeXePuz4zo2LMw==}
    engines: {node: '>=6.9.0'}
    peerDependencies:
      '@babel/core': ^7.0.0-0

  '@babel/plugin-transform-unicode-regex@7.29.7':
    resolution: {integrity: sha512-7D/x/23/d/3VqZ0QA+LGbZMlGwZjztBygSWWWsfTPoQ1oQ6Q1P6Mr3d0kk42XabyUVw+fha3LqdRsFqeKqvCyA==}
    engines: {node: '>=6.9.0'}
    peerDependencies:
      '@babel/core': ^7.0.0-0

  '@babel/preset-react@7.29.7':
    resolution: {integrity: sha512-C+PV1TFUPTmBQGoPBL8j2QmLpZ117YTCwxIZeJOM96GbYMFSc7/pOXU5lVykwnZxyTqQxRsvoRk6f2FktZgGHA==}
    engines: {node: '>=6.9.0'}
    peerDependencies:
      '@babel/core': ^7.0.0-0

  '@babel/preset-typescript@7.29.7':
    resolution: {integrity: sha512-/Foi8vKY2EVbed/1eZx0gJEEwHAIxogrySI7rULcRIvhZzbvoE/b5qG5Ghc0WKAFKOHA9SD1x7RsFlOYdutIiQ==}
    engines: {node: '>=6.9.0'}
    peerDependencies:
      '@babel/core': ^7.0.0-0

  '@babel/runtime@7.29.7':
    resolution: {integrity: sha512-Nq8OhGWiZIZGV6hLHoyAKLLcJihP/xFeBMGJoUrxTX2psI8dCifzLhZISFb+VWS3wFMRDmCGw5R+dOySCqPLhw==}
    engines: {node: '>=6.9.0'}

  '@babel/template@7.29.7':
    resolution: {integrity: sha512-puq+Gf35oI24FeN11LkoUQFqv9uwNeWpxXZi/Ji3rRIoKAzKnxRaZ+Gkj0vKS9ZCiTESfng1N9LyOyXvo+m+Gg==}
    engines: {node: '>=6.9.0'}

  '@babel/traverse@7.29.7':
    resolution: {integrity: sha512-EhlfNQtZ+NK22w5BM61ciuiq1m58ed33Wr1Xan//ZRTy6hgjnwyCffRYwzsGXdASJSUJ1guZILsErh1eQcl+zw==}
    engines: {node: '>=6.9.0'}

  '@babel/types@7.29.7':
    resolution: {integrity: sha512-4zBIxpPzowiZpusoFkyGVwakdRJUyuH5PxQ/PrqghfdFWWasvnCdPfQXHrenDai+gyLARulZjZowCOj6fjT4pA==}
    engines: {node: '>=6.9.0'}

  '@bcoe/v8-coverage@0.2.3':
    resolution: {integrity: sha512-0hYQ8SB4Db5zvZB4axdMHGwEaQjkZzFjQiN9LVYvIFB2nSUHW9tYpxWriPrWDASIxiaXax83REcLxuSdnGPZtw==}

  '@emnapi/core@1.10.0':
    resolution: {integrity: sha512-yq6OkJ4p82CAfPl0u9mQebQHKPJkY7WrIuk205cTYnYe+k2Z8YBh11FrbRG/H6ihirqcacOgl2BIO8oyMQLeXw==}

  '@emnapi/runtime@1.10.0':
    resolution: {integrity: sha512-ewvYlk86xUoGI0zQRNq/mC+16R1QeDlKQy21Ki3oSYXNgLb45GV1P6A0M+/s6nyCuNDqe5VpaY84BzXGwVbwFA==}

  '@emnapi/runtime@1.11.0':
    resolution: {integrity: sha512-55coeOFKHv1ywEcUXJtWU5f+Jr/W5tZDvZig8DLKSwUN1JpROQ4rk/SNOQiFWmaR/VKF4zuFyW1B8JduOSv6Pg==}

  '@emnapi/wasi-threads@1.2.1':
    resolution: {integrity: sha512-uTII7OYF+/Mes/MrcIOYp5yOtSMLBWSIoLPpcgwipoiKbli6k322tcoFsxoIIxPDqW01SQGAgko4EzZi2BNv2w==}

  '@eslint-community/eslint-utils@4.9.1':
    resolution: {integrity: sha512-phrYmNiYppR7znFEdqgfWHXR6NCkZEK7hwWDHZUjit/2/U0r6XvkDl0SYnoM51Hq7FhCGdLDT6zxCCOY1hexsQ==}
    engines: {node: ^12.22.0 || ^14.17.0 || >=16.0.0}
    peerDependencies:
      eslint: ^6.0.0 || ^7.0.0 || >=8.0.0

  '@eslint-community/regexpp@4.12.2':
    resolution: {integrity: sha512-EriSTlt5OC9/7SXkRSCAhfSxxoSUgBm33OH+IkwbdpgoqsSsUg7y3uh+IICI/Qg4BBWr3U2i39RpmycbxMq4ew==}
    engines: {node: ^12.0.0 || ^14.0.0 || >=16.0.0}

  '@eslint/eslintrc@2.1.4':
    resolution: {integrity: sha512-269Z39MS6wVJtsoUl10L60WdkhJVdPG24Q4eZTH3nnF6lpvSShEK3wQjDX9JRWAUPvPh7COouPpU9IrqaZFvtQ==}
    engines: {node: ^12.22.0 || ^14.17.0 || >=16.0.0}

  '@eslint/js@8.57.1':
    resolution: {integrity: sha512-d9zaMRSTIKDLhctzH12MtXvJKSSUhaHcjV+2Z+GK+EEY7XKpP5yR4x+N3TAcHTcu963nIr+TMcCb4DBCYX1z6Q==}
    engines: {node: ^12.22.0 || ^14.17.0 || >=16.0.0}

  '@expo-google-fonts/jetbrains-mono@0.4.1':
    resolution: {integrity: sha512-CslACrtMOcRwoWXCO7OMEI+9w3fukWSoBtvNz46OqPoogEuuoY0tkDY1O8sFumk8t0pC6Cx0Xr95O0TOQhpkug==}

  '@expo-google-fonts/material-symbols@0.4.38':
    resolution: {integrity: sha512-IJkBtN1o8u9BW5fvSii1MyHPQ7Q0HxbWcVBvOrOzgMLpVtZw7R2w94wBTVR7kZwv3w1JNTESMmLA5Sqn1+Z36A==}

  '@expo-google-fonts/montserrat@0.4.2':
    resolution: {integrity: sha512-Xyq7rKJhhZOE1Xk4wKSSVoUeOkFmQEMhtZ3pdFrgYckGZMs115Apmld1AI8Ju+yrl5GzDdfRCCqRr33dvEDYUA==}

  '@expo-google-fonts/outfit@0.4.3':
    resolution: {integrity: sha512-2uQmDVJencWLllxds6SG92E+SjxyZfvg7eZKZ5XLHggmm5AuUyQK7lzMAFOUzT6kheq2kJ7BAiubMdjKT32fJg==}

  '@expo/cli@54.0.25':
    resolution: {integrity: sha512-WnUqIb8oMBhtwSfIqdCHCzcaDIpLNXItRVd5miuvWi4GO0SGo89PSsAkbVJ+LJgcaY+v5rbgMELJS9I/CqOulA==}
    hasBin: true
    peerDependencies:
      expo: '*'
      expo-router: '*'
      react-native: '*'
    peerDependenciesMeta:
      expo-router:
        optional: true
      react-native:
        optional: true

  '@expo/code-signing-certificates@0.0.6':
    resolution: {integrity: sha512-iNe0puxwBNEcuua9gmTGzq+SuMDa0iATai1FlFTMHJ/vUmKvN/V//drXoLJkVb5i5H3iE/n/qIJxyoBnXouD0w==}

  '@expo/config-plugins@54.0.4':
    resolution: {integrity: sha512-g2yXGICdoOw5i3LkQSDxl2Q5AlQCrG7oniu0pCPPO+UxGb7He4AFqSvPSy8HpRUj55io17hT62FTjYRD+d6j3Q==}

  '@expo/config-types@54.0.10':
    resolution: {integrity: sha512-/J16SC2an1LdtCZ67xhSkGXpALYUVUNyZws7v+PVsFZxClYehDSoKLqyRaGkpHlYrCc08bS0RF5E0JV6g50psA==}

  '@expo/config@12.0.13':
    resolution: {integrity: sha512-Cu52arBa4vSaupIWsF0h7F/Cg//N374nYb7HAxV0I4KceKA7x2UXpYaHOL7EEYYvp7tZdThBjvGpVmr8ScIvaQ==}

  '@expo/devcert@1.2.1':
    resolution: {integrity: sha512-qC4eaxmKMTmJC2ahwyui6ud8f3W60Ss7pMkpBq40Hu3zyiAaugPXnZ24145U7K36qO9UHdZUVxsCvIpz2RYYCA==}

  '@expo/devtools@0.1.8':
    resolution: {integrity: sha512-SVLxbuanDjJPgc0sy3EfXUMLb/tXzp6XIHkhtPVmTWJAp+FOr6+5SeiCfJrCzZFet0Ifyke2vX3sFcKwEvCXwQ==}
    peerDependencies:
      react: '*'
      react-native: '*'
    peerDependenciesMeta:
      react:
        optional: true
      react-native:
        optional: true

  '@expo/dom-webview@56.0.5':
    resolution: {integrity: sha512-UIEJxkLg6cHqofKrpWpkn9E6ApxVRtCgZhZkARPr9VV7rBVloJgeroTHs31YgU/JpbI5lLQOnfOlGo54W6C2Ew==}
    peerDependencies:
      expo: '*'
      react: '*'
      react-native: '*'

  '@expo/env@2.0.11':
    resolution: {integrity: sha512-xV+ps6YCW7XIPVUwFVCRN2nox09dnRwy8uIjwHWTODu0zFw4kp4omnVkl0OOjuu2XOe7tdgAHxikrkJt9xB/7Q==}

  '@expo/fingerprint@0.15.5':
    resolution: {integrity: sha512-mdVoAMcux1WlM6kd1RoWiHRNqKqS+J6mKmWQ/BKgeh937S/fcW58EE68O6nc4KDXtWi3PBeNHskOFcgyIuD4hw==}
    hasBin: true

  '@expo/image-utils@0.8.14':
    resolution: {integrity: sha512-5Sn+jG4Cw+shC2wDMXoqSAJnvERbiwzHn05FpWtD5IBflfTIs5gUmjzwiGVyjOdlMSQhgRrw/AymPbmO9h9mpQ==}

  '@expo/json-file@10.0.16':
    resolution: {integrity: sha512-fcVkWEj+hLuP2yt5W0aw6LmDRqSPWDLUSxOMcmFeV+algmIF59sQVKCwB9btjQLd4V6x9N0pISkQEkBubUHrCw==}

  '@expo/json-file@10.2.0':
    resolution: {integrity: sha512-S6XzKe3R9GQeHiUPXc3xJjOv2VJhOEwFYf7xdC2z2cUqt3kZJ9mSO877sNQloVdnW/SUCtPY3bexlM7nwq+CAQ==}

  '@expo/log-box@56.0.12':
    resolution: {integrity: sha512-budE6AGmJbpOJfGSOz+JVP3+FevElT82IEIg+ukQ4gZpW/dGO7QX1unFjanKdSaYgudBwJ4FCFGMwWhW/1tXVQ==}
    peerDependencies:
      '@expo/dom-webview': ^56.0.5
      expo: '*'
      react: '*'
      react-native: '*'

  '@expo/metro-config@54.0.16':
    resolution: {integrity: sha512-3LLb9ZQl0VlqSlsalJ7+CYjfz60PBoSDHvpE1UF71aTM1Nx0Vb4LhXo7bCCC+PYP9q/GPB58LLbIROQ8PjKX2w==}
    peerDependencies:
      expo: '*'
    peerDependenciesMeta:
      expo:
        optional: true

  '@expo/metro-runtime@6.1.2':
    resolution: {integrity: sha512-nvM+Qv45QH7pmYvP8JB1G8JpScrWND3KrMA6ZKe62cwwNiX/BjHU28Ear0v/4bQWXlOY0mv6B8CDIm8JxXde9g==}
    peerDependencies:
      expo: '*'
      react: '*'
      react-dom: '*'
      react-native: '*'
    peerDependenciesMeta:
      react-dom:
        optional: true

  '@expo/metro@54.2.0':
    resolution: {integrity: sha512-h68TNZPGsk6swMmLm9nRSnE2UXm48rWwgcbtAHVMikXvbxdS41NDHHeqg1rcQ9AbznDRp6SQVC2MVpDnsRKU1w==}

  '@expo/osascript@2.6.0':
    resolution: {integrity: sha512-QvqDBlJXa8CS2vRORJ4wEflY1m0vVI07uSJdIRgBrLxRPBcsrXxrtU7+wXRXMqfq9zLwNP9XbvRsXF2omoDylg==}
    engines: {node: '>=12'}

  '@expo/package-manager@1.12.1':
    resolution: {integrity: sha512-fQLiFAcFRWF53mtuLK32SUJQ1ahhrTcBZPZPedYTiUT5ha5FF+UO6bPtCc0Y/hgj0/m3HCGBAuSHjbg2kI9oPQ==}

  '@expo/plist@0.4.9':
    resolution: {integrity: sha512-MPVpmKGfnQEnrCzgxuXcmPP/y/t6AVm+DcSb2Myp21LKWv1N3l8uFxMggesfF4ixAxkRlGmMMx9GyDC9M+XklQ==}

  '@expo/prebuild-config@54.0.8':
    resolution: {integrity: sha512-EA7N4dloty2t5Rde+HP0IEE+nkAQiu4A/+QGZGT9mFnZ5KKjPPkqSyYcRvP5bhQE10D+tvz6X0ngZpulbMdbsg==}
    peerDependencies:
      expo: '*'

  '@expo/require-utils@55.0.5':
    resolution: {integrity: sha512-U4K/CQ2VpXuwfNGsN+daKmYOt15hCP8v/pXaYH6eut7kdYZo6SfJ1yr67BIcJ+1Gzzs+QzTxswAZChKpXmceyw==}
    peerDependencies:
      typescript: ^5.0.0 || ^5.0.0-0
    peerDependenciesMeta:
      typescript:
        optional: true

  '@expo/schema-utils@0.1.8':
    resolution: {integrity: sha512-9I6ZqvnAvKKDiO+ZF8BpQQFYWXOJvTAL5L/227RUbWG1OVZDInFifzCBiqAZ3b67NRfeAgpgvbA7rejsqhY62A==}

  '@expo/schema-utils@56.0.1':
    resolution: {integrity: sha512-CZ/+mYbQmWeOnkCGlWy9K+lFxbJSMFY7+TqBZcKzBSTU5Q7IGRvn/sOG3TdNjIdLPmbA8xe7R/c3UUQ28R9i9w==}

  '@expo/sdk-runtime-versions@1.0.0':
    resolution: {integrity: sha512-Doz2bfiPndXYFPMRwPyGa1k5QaKDVpY806UJj570epIiMzWaYyCtobasyfC++qfIXVb5Ocy7r3tP9d62hAQ7IQ==}

  '@expo/spawn-async@1.8.0':
    resolution: {integrity: sha512-eb9xxd/LbuEGSdua4NumCu/McVB9EM+F/JxB9pWgnERw4HQ9XyTNH1KapG6oqLWR8TuRK2LQfzJlmNi94CVobw==}
    engines: {node: '>=12'}

  '@expo/sudo-prompt@9.3.2':
    resolution: {integrity: sha512-HHQigo3rQWKMDzYDLkubN5WQOYXJJE2eNqIQC2axC2iO3mHdwnIR7FgZVvHWtBwAdzBgAP0ECp8KqS8TiMKvgw==}

  '@expo/ui@56.0.16':
    resolution: {integrity: sha512-NPbpseOC4VNoDvOBgGtTb63fu2IfdnxNwp9K8pqU2mBTQPxEMcxF0ijgNBJ0Ze1NEuLJoBhJyrHWoj3zRmovkA==}
    peerDependencies:
      '@babel/core': '*'
      expo: '*'
      react: '*'
      react-dom: '*'
      react-native: '*'
      react-native-reanimated: '*'
      react-native-worklets: '*'
    peerDependenciesMeta:
      '@babel/core':
        optional: true
      react-dom:
        optional: true
      react-native-reanimated:
        optional: true
      react-native-worklets:
        optional: true

  '@expo/vector-icons@15.1.1':
    resolution: {integrity: sha512-Iu2VkcoI5vygbtYngm7jb4ifxElNVXQYdDrYkT7UCEIiKLeWnQY0wf2ZhHZ+Wro6Sc5TaumpKUOqDRpLi5rkvw==}
    peerDependencies:
      expo-font: '>=14.0.4'
      react: '*'
      react-native: '*'

  '@expo/ws-tunnel@1.0.6':
    resolution: {integrity: sha512-nDRbLmSrJar7abvUjp3smDwH8HcbZcoOEa5jVPUv9/9CajgmWw20JNRwTuBRzWIWIkEJDkz20GoNA+tSwUqk0Q==}

  '@expo/xcpretty@4.4.4':
    resolution: {integrity: sha512-4aQzz9vgxcNXFfo/iyNgDDYfsU5XGKKxWxZopw0cVotHiW+U8IJbIxMaxsINs6bHhtkG3StKNPcOrn3eBuxKPw==}
    hasBin: true

  '@humanwhocodes/config-array@0.13.0':
    resolution: {integrity: sha512-DZLEEqFWQFiyK6h5YIeynKx7JlvCYWL0cImfSRXZ9l4Sg2efkFGTuFf6vzXjK1cq6IYkU+Eg/JizXw+TD2vRNw==}
    engines: {node: '>=10.10.0'}
    deprecated: Use @eslint/config-array instead

  '@humanwhocodes/module-importer@1.0.1':
    resolution: {integrity: sha512-bxveV4V8v5Yb4ncFTT3rPSgZBOpCkjfK0y4oVVVJwIuDVBRMDXrPyXRL988i5ap9m9bnyEEjWfm5WkBmtffLfA==}
    engines: {node: '>=12.22'}

  '@humanwhocodes/object-schema@2.0.3':
    resolution: {integrity: sha512-93zYdMES/c1D69yZiKDBj0V24vqNzB/koF26KPaagAfd3P/4gUlh3Dys5ogAK+Exi9QyzlD8x/08Zt7wIKcDcA==}
    deprecated: Use @eslint/object-schema instead

  '@ide/backoff@1.0.0':
    resolution: {integrity: sha512-F0YfUDjvT+Mtt/R4xdl2X0EYCHMMiJqNLdxHD++jDT5ydEFIyqbCHh51Qx2E211dgZprPKhV7sHmnXKpLuvc5g==}

  '@img/colour@1.1.0':
    resolution: {integrity: sha512-Td76q7j57o/tLVdgS746cYARfSyxk8iEfRxewL9h4OMzYhbW4TAcppl0mT4eyqXddh6L/jwoM75mo7ixa/pCeQ==}
    engines: {node: '>=18'}

  '@img/sharp-darwin-arm64@0.34.5':
    resolution: {integrity: sha512-imtQ3WMJXbMY4fxb/Ndp6HBTNVtWCUI0WdobyheGf5+ad6xX8VIDO8u2xE4qc/fr08CKG/7dDseFtn6M6g/r3w==}
    engines: {node: ^18.17.0 || ^20.3.0 || >=21.0.0}
    cpu: [arm64]
    os: [darwin]

  '@img/sharp-darwin-x64@0.34.5':
    resolution: {integrity: sha512-YNEFAF/4KQ/PeW0N+r+aVVsoIY0/qxxikF2SWdp+NRkmMB7y9LBZAVqQ4yhGCm/H3H270OSykqmQMKLBhBJDEw==}
    engines: {node: ^18.17.0 || ^20.3.0 || >=21.0.0}
    cpu: [x64]
    os: [darwin]

  '@img/sharp-libvips-darwin-arm64@1.2.4':
    resolution: {integrity: sha512-zqjjo7RatFfFoP0MkQ51jfuFZBnVE2pRiaydKJ1G/rHZvnsrHAOcQALIi9sA5co5xenQdTugCvtb1cuf78Vf4g==}
    cpu: [arm64]
    os: [darwin]

  '@img/sharp-libvips-darwin-x64@1.2.4':
    resolution: {integrity: sha512-1IOd5xfVhlGwX+zXv2N93k0yMONvUlANylbJw1eTah8K/Jtpi15KC+WSiaX/nBmbm2HxRM1gZ0nSdjSsrZbGKg==}
    cpu: [x64]
    os: [darwin]

  '@img/sharp-libvips-linux-arm64@1.2.4':
    resolution: {integrity: sha512-excjX8DfsIcJ10x1Kzr4RcWe1edC9PquDRRPx3YVCvQv+U5p7Yin2s32ftzikXojb1PIFc/9Mt28/y+iRklkrw==}
    cpu: [arm64]
    os: [linux]

  '@img/sharp-libvips-linux-arm@1.2.4':
    resolution: {integrity: sha512-bFI7xcKFELdiNCVov8e44Ia4u2byA+l3XtsAj+Q8tfCwO6BQ8iDojYdvoPMqsKDkuoOo+X6HZA0s0q11ANMQ8A==}
    cpu: [arm]
    os: [linux]

  '@img/sharp-libvips-linux-ppc64@1.2.4':
    resolution: {integrity: sha512-FMuvGijLDYG6lW+b/UvyilUWu5Ayu+3r2d1S8notiGCIyYU/76eig1UfMmkZ7vwgOrzKzlQbFSuQfgm7GYUPpA==}
    cpu: [ppc64]
    os: [linux]

  '@img/sharp-libvips-linux-riscv64@1.2.4':
    resolution: {integrity: sha512-oVDbcR4zUC0ce82teubSm+x6ETixtKZBh/qbREIOcI3cULzDyb18Sr/Wcyx7NRQeQzOiHTNbZFF1UwPS2scyGA==}
    cpu: [riscv64]
    os: [linux]

  '@img/sharp-libvips-linux-s390x@1.2.4':
    resolution: {integrity: sha512-qmp9VrzgPgMoGZyPvrQHqk02uyjA0/QrTO26Tqk6l4ZV0MPWIW6LTkqOIov+J1yEu7MbFQaDpwdwJKhbJvuRxQ==}
    cpu: [s390x]
    os: [linux]

  '@img/sharp-libvips-linux-x64@1.2.4':
    resolution: {integrity: sha512-tJxiiLsmHc9Ax1bz3oaOYBURTXGIRDODBqhveVHonrHJ9/+k89qbLl0bcJns+e4t4rvaNBxaEZsFtSfAdquPrw==}
    cpu: [x64]
    os: [linux]

  '@img/sharp-libvips-linuxmusl-arm64@1.2.4':
    resolution: {integrity: sha512-FVQHuwx1IIuNow9QAbYUzJ+En8KcVm9Lk5+uGUQJHaZmMECZmOlix9HnH7n1TRkXMS0pGxIJokIVB9SuqZGGXw==}
    cpu: [arm64]
    os: [linux]

  '@img/sharp-libvips-linuxmusl-x64@1.2.4':
    resolution: {integrity: sha512-+LpyBk7L44ZIXwz/VYfglaX/okxezESc6UxDSoyo2Ks6Jxc4Y7sGjpgU9s4PMgqgjj1gZCylTieNamqA1MF7Dg==}
    cpu: [x64]
    os: [linux]

  '@img/sharp-linux-arm64@0.34.5':
    resolution: {integrity: sha512-bKQzaJRY/bkPOXyKx5EVup7qkaojECG6NLYswgktOZjaXecSAeCWiZwwiFf3/Y+O1HrauiE3FVsGxFg8c24rZg==}
    engines: {node: ^18.17.0 || ^20.3.0 || >=21.0.0}
    cpu: [arm64]
    os: [linux]

  '@img/sharp-linux-arm@0.34.5':
    resolution: {integrity: sha512-9dLqsvwtg1uuXBGZKsxem9595+ujv0sJ6Vi8wcTANSFpwV/GONat5eCkzQo/1O6zRIkh0m/8+5BjrRr7jDUSZw==}
    engines: {node: ^18.17.0 || ^20.3.0 || >=21.0.0}
    cpu: [arm]
    os: [linux]

  '@img/sharp-linux-ppc64@0.34.5':
    resolution: {integrity: sha512-7zznwNaqW6YtsfrGGDA6BRkISKAAE1Jo0QdpNYXNMHu2+0dTrPflTLNkpc8l7MUP5M16ZJcUvysVWWrMefZquA==}
    engines: {node: ^18.17.0 || ^20.3.0 || >=21.0.0}
    cpu: [ppc64]
    os: [linux]

  '@img/sharp-linux-riscv64@0.34.5':
    resolution: {integrity: sha512-51gJuLPTKa7piYPaVs8GmByo7/U7/7TZOq+cnXJIHZKavIRHAP77e3N2HEl3dgiqdD/w0yUfiJnII77PuDDFdw==}
    engines: {node: ^18.17.0 || ^20.3.0 || >=21.0.0}
    cpu: [riscv64]
    os: [linux]

  '@img/sharp-linux-s390x@0.34.5':
    resolution: {integrity: sha512-nQtCk0PdKfho3eC5MrbQoigJ2gd1CgddUMkabUj+rBevs8tZ2cULOx46E7oyX+04WGfABgIwmMC0VqieTiR4jg==}
    engines: {node: ^18.17.0 || ^20.3.0 || >=21.0.0}
    cpu: [s390x]
    os: [linux]

  '@img/sharp-linux-x64@0.34.5':
    resolution: {integrity: sha512-MEzd8HPKxVxVenwAa+JRPwEC7QFjoPWuS5NZnBt6B3pu7EG2Ge0id1oLHZpPJdn3OQK+BQDiw9zStiHBTJQQQQ==}
    engines: {node: ^18.17.0 || ^20.3.0 || >=21.0.0}
    cpu: [x64]
    os: [linux]

  '@img/sharp-linuxmusl-arm64@0.34.5':
    resolution: {integrity: sha512-fprJR6GtRsMt6Kyfq44IsChVZeGN97gTD331weR1ex1c1rypDEABN6Tm2xa1wE6lYb5DdEnk03NZPqA7Id21yg==}
    engines: {node: ^18.17.0 || ^20.3.0 || >=21.0.0}
    cpu: [arm64]
    os: [linux]

  '@img/sharp-linuxmusl-x64@0.34.5':
    resolution: {integrity: sha512-Jg8wNT1MUzIvhBFxViqrEhWDGzqymo3sV7z7ZsaWbZNDLXRJZoRGrjulp60YYtV4wfY8VIKcWidjojlLcWrd8Q==}
    engines: {node: ^18.17.0 || ^20.3.0 || >=21.0.0}
    cpu: [x64]
    os: [linux]

  '@img/sharp-wasm32@0.34.5':
    resolution: {integrity: sha512-OdWTEiVkY2PHwqkbBI8frFxQQFekHaSSkUIJkwzclWZe64O1X4UlUjqqqLaPbUpMOQk6FBu/HtlGXNblIs0huw==}
    engines: {node: ^18.17.0 || ^20.3.0 || >=21.0.0}
    cpu: [wasm32]

  '@img/sharp-win32-arm64@0.34.5':
    resolution: {integrity: sha512-WQ3AgWCWYSb2yt+IG8mnC6Jdk9Whs7O0gxphblsLvdhSpSTtmu69ZG1Gkb6NuvxsNACwiPV6cNSZNzt0KPsw7g==}
    engines: {node: ^18.17.0 || ^20.3.0 || >=21.0.0}
    cpu: [arm64]
    os: [win32]

  '@img/sharp-win32-ia32@0.34.5':
    resolution: {integrity: sha512-FV9m/7NmeCmSHDD5j4+4pNI8Cp3aW+JvLoXcTUo0IqyjSfAZJ8dIUmijx1qaJsIiU+Hosw6xM5KijAWRJCSgNg==}
    engines: {node: ^18.17.0 || ^20.3.0 || >=21.0.0}
    cpu: [ia32]
    os: [win32]

  '@img/sharp-win32-x64@0.34.5':
    resolution: {integrity: sha512-+29YMsqY2/9eFEiW93eqWnuLcWcufowXewwSNIT6UwZdUUCrM3oFjMWH/Z6/TMmb4hlFenmfAVbpWeup2jryCw==}
    engines: {node: ^18.17.0 || ^20.3.0 || >=21.0.0}
    cpu: [x64]
    os: [win32]

  '@isaacs/fs-minipass@4.0.1':
    resolution: {integrity: sha512-wgm9Ehl2jpeqP3zw/7mo3kRHFp5MEDhqAdwy1fTGkHAwnkGOVsgpvQhL8B5n1qlb01jV3n/bI0ZfZp5lWA1k4w==}
    engines: {node: '>=18.0.0'}

  '@isaacs/ttlcache@1.4.1':
    resolution: {integrity: sha512-RQgQ4uQ+pLbqXfOmieB91ejmLwvSgv9nLx6sT6sD83s7umBypgg+OIBOBbEUiJXrfpnp9j0mRhYYdzp9uqq3lA==}
    engines: {node: '>=12'}

  '@istanbuljs/load-nyc-config@1.1.0':
    resolution: {integrity: sha512-VjeHSlIzpv/NyD3N0YuHfXOPDIixcA1q2ZV98wsMqcYlPmv2n3Yb2lYP9XMElnaFVXg5A7YLTeLu6V84uQDjmQ==}
    engines: {node: '>=8'}

  '@istanbuljs/schema@0.1.6':
    resolution: {integrity: sha512-+Sg6GCR/wy1oSmQDFq4LQDAhm3ETKnorxN+y5nbLULOR3P0c14f2Wurzj3/xqPXtasLFfHd5iRFQ7AJt4KH2cw==}
    engines: {node: '>=8'}

  '@jest/console@29.7.0':
    resolution: {integrity: sha512-5Ni4CU7XHQi32IJ398EEP4RrB8eV09sXP2ROqD4bksHrnTree52PsxvX8tpL8LvTZ3pFzXyPbNQReSN41CAhOg==}
    engines: {node: ^14.15.0 || ^16.10.0 || >=18.0.0}

  '@jest/core@29.7.0':
    resolution: {integrity: sha512-n7aeXWKMnGtDA48y8TLWJPJmLmmZ642Ceo78cYWEpiD7FzDgmNDV/GCVRorPABdXLJZ/9wzzgZAlHjXjxDHGsg==}
    engines: {node: ^14.15.0 || ^16.10.0 || >=18.0.0}
    peerDependencies:
      node-notifier: ^8.0.1 || ^9.0.0 || ^10.0.0
    peerDependenciesMeta:
      node-notifier:
        optional: true

  '@jest/create-cache-key-function@29.7.0':
    resolution: {integrity: sha512-4QqS3LY5PBmTRHj9sAg1HLoPzqAI0uOX6wI/TRqHIcOxlFidy6YEmCQJk6FSZjNLGCeubDMfmkWL+qaLKhSGQA==}
    engines: {node: ^14.15.0 || ^16.10.0 || >=18.0.0}

  '@jest/environment@29.7.0':
    resolution: {integrity: sha512-aQIfHDq33ExsN4jP1NWGXhxgQ/wixs60gDiKO+XVMd8Mn0NWPWgc34ZQDTb2jKaUWQ7MuwoitXAsN2XVXNMpAw==}
    engines: {node: ^14.15.0 || ^16.10.0 || >=18.0.0}

  '@jest/expect-utils@29.7.0':
    resolution: {integrity: sha512-GlsNBWiFQFCVi9QVSx7f5AgMeLxe9YCCs5PuP2O2LdjDAA8Jh9eX7lA1Jq/xdXw3Wb3hyvlFNfZIfcRetSzYcA==}
    engines: {node: ^14.15.0 || ^16.10.0 || >=18.0.0}

  '@jest/expect@29.7.0':
    resolution: {integrity: sha512-8uMeAMycttpva3P1lBHB8VciS9V0XAr3GymPpipdyQXbBcuhkLQOSe8E/p92RyAdToS6ZD1tFkX+CkhoECE0dQ==}
    engines: {node: ^14.15.0 || ^16.10.0 || >=18.0.0}

  '@jest/fake-timers@29.7.0':
    resolution: {integrity: sha512-q4DH1Ha4TTFPdxLsqDXK1d3+ioSL7yL5oCMJZgDYm6i+6CygW5E5xVr/D1HdsGxjt1ZWSfUAs9OxSB/BNelWrQ==}
    engines: {node: ^14.15.0 || ^16.10.0 || >=18.0.0}

  '@jest/globals@29.7.0':
    resolution: {integrity: sha512-mpiz3dutLbkW2MNFubUGUEVLkTGiqW6yLVTA+JbP6fI6J5iL9Y0Nlg8k95pcF8ctKwCS7WVxteBs29hhfAotzQ==}
    engines: {node: ^14.15.0 || ^16.10.0 || >=18.0.0}

  '@jest/reporters@29.7.0':
    resolution: {integrity: sha512-DApq0KJbJOEzAFYjHADNNxAE3KbhxQB1y5Kplb5Waqw6zVbuWatSnMjE5gs8FUgEPmNsnZA3NCWl9NG0ia04Pg==}
    engines: {node: ^14.15.0 || ^16.10.0 || >=18.0.0}
    peerDependencies:
      node-notifier: ^8.0.1 || ^9.0.0 || ^10.0.0
    peerDependenciesMeta:
      node-notifier:
        optional: true

  '@jest/schemas@29.6.3':
    resolution: {integrity: sha512-mo5j5X+jIZmJQveBKeS/clAueipV7KgiX1vMgCxam1RNYiqE1w62n0/tJJnHtjW8ZHcQco5gY85jA3mi0L+nSA==}
    engines: {node: ^14.15.0 || ^16.10.0 || >=18.0.0}

  '@jest/source-map@29.6.3':
    resolution: {integrity: sha512-MHjT95QuipcPrpLM+8JMSzFx6eHp5Bm+4XeFDJlwsvVBjmKNiIAvasGK2fxz2WbGRlnvqehFbh07MMa7n3YJnw==}
    engines: {node: ^14.15.0 || ^16.10.0 || >=18.0.0}

  '@jest/test-result@29.7.0':
    resolution: {integrity: sha512-Fdx+tv6x1zlkJPcWXmMDAG2HBnaR9XPSd5aDWQVsfrZmLVT3lU1cwyxLgRmXR9yrq4NBoEm9BMsfgFzTQAbJYA==}
    engines: {node: ^14.15.0 || ^16.10.0 || >=18.0.0}

  '@jest/test-sequencer@29.7.0':
    resolution: {integrity: sha512-GQwJ5WZVrKnOJuiYiAF52UNUJXgTZx1NHjFSEB0qEMmSZKAkdMoIzw/Cj6x6NF4AvV23AUqDpFzQkN/eYCYTxw==}
    engines: {node: ^14.15.0 || ^16.10.0 || >=18.0.0}

  '@jest/transform@29.7.0':
    resolution: {integrity: sha512-ok/BTPFzFKVMwO5eOHRrvnBVHdRy9IrsrW1GpMaQ9MCnilNLXQKmAX8s1YXDFaai9xJpac2ySzV0YeRRECr2Vw==}
    engines: {node: ^14.15.0 || ^16.10.0 || >=18.0.0}

  '@jest/types@29.6.3':
    resolution: {integrity: sha512-u3UPsIilWKOM3F9CXtrG8LEJmNxwoCQC/XVj4IKYXvvpx7QIi/Kg1LI5uDmDpKlac62NUtX7eLjRh+jVZcLOzw==}
    engines: {node: ^14.15.0 || ^16.10.0 || >=18.0.0}

  '@jridgewell/gen-mapping@0.3.13':
    resolution: {integrity: sha512-2kkt/7niJ6MgEPxF0bYdQ6etZaA+fQvDcLKckhy1yIQOzaoKjBBjSj63/aLVjYE3qhRt5dvM+uUyfCg6UKCBbA==}

  '@jridgewell/remapping@2.3.5':
    resolution: {integrity: sha512-LI9u/+laYG4Ds1TDKSJW2YPrIlcVYOwi2fUC6xB43lueCjgxV4lffOCZCtYFiH6TNOX+tQKXx97T4IKHbhyHEQ==}

  '@jridgewell/resolve-uri@3.1.2':
    resolution: {integrity: sha512-bRISgCIjP20/tbWSPWMEi54QVPRZExkuD9lJL+UIxUKtwVJA8wW1Trb1jMs1RFXo1CBTNZ/5hpC9QvmKWdopKw==}
    engines: {node: '>=6.0.0'}

  '@jridgewell/source-map@0.3.11':
    resolution: {integrity: sha512-ZMp1V8ZFcPG5dIWnQLr3NSI1MiCU7UETdS/A0G8V/XWHvJv3ZsFqutJn1Y5RPmAPX6F3BiE397OqveU/9NCuIA==}

  '@jridgewell/sourcemap-codec@1.5.5':
    resolution: {integrity: sha512-cYQ9310grqxueWbl+WuIUIaiUaDcj7WOq5fVhEljNVgRfOUhY9fy2zTvfoqWsnebh8Sl70VScFbICvJnLKB0Og==}

  '@jridgewell/trace-mapping@0.3.31':
    resolution: {integrity: sha512-zzNR+SdQSDJzc8joaeP8QQoCQr8NuYx2dIIytl1QeBEZHJ9uW6hebsrYgbz8hJwUQao3TWCMtmfV8Nu1twOLAw==}

  '@napi-rs/wasm-runtime@1.1.4':
    resolution: {integrity: sha512-3NQNNgA1YSlJb/kMH1ildASP9HW7/7kYnRI2szWJaofaS1hWmbGI4H+d3+22aGzXXN9IJ+n+GiFVcGipJP18ow==}
    peerDependencies:
      '@emnapi/core': ^1.7.1
      '@emnapi/runtime': ^1.7.1

  '@next/env@15.5.19':
    resolution: {integrity: sha512-sWWluFvcv5v3Fxznmf2ZfjyoVQt/64oCnYqS90inQWGzMPK1VjvekPiz3OPHKmFT30EnHrjlbyaHLt3M0vWabw==}

  '@next/swc-darwin-arm64@15.5.19':
    resolution: {integrity: sha512-jx9wWlTKueHKPvVOndyr7WuaevWCkuYqsQ8gC0TMPKAVWG3MhcdMrjfo9tvIZNXd0QOUYXXvAcZ325y8Uq7uzg==}
    engines: {node: '>= 10'}
    cpu: [arm64]
    os: [darwin]

  '@next/swc-darwin-x64@15.5.19':
    resolution: {integrity: sha512-291KFcsIQ3OenRdiUDFOR6W3wezzH4auENXm1gbm1Bjd4ANMMRgxPrWTUztQN43BnVoVuMnHCrLeECIMwgFKbA==}
    engines: {node: '>= 10'}
    cpu: [x64]
    os: [darwin]

  '@next/swc-linux-arm64-gnu@15.5.19':
    resolution: {integrity: sha512-WeH+nelQyyMeE2f8FxBRZNrGipya5zHZV2vjzfCOAYyiI6am+NbnWAAldOBFQBB2w0DjJcsvrKqoFT2b7+5YoA==}
    engines: {node: '>= 10'}
    cpu: [arm64]
    os: [linux]

  '@next/swc-linux-arm64-musl@15.5.19':
    resolution: {integrity: sha512-5xTOE0lDlDCSSfp+BAif7j17VRRCjWp//ZPZy6NI0QpdrhxtQnsZguSx0xAAZ0c9XZLrLLwCe/XVe5YPrRilKw==}
    engines: {node: '>= 10'}
    cpu: [arm64]
    os: [linux]

  '@next/swc-linux-x64-gnu@15.5.19':
    resolution: {integrity: sha512-LTxRmMgqqMv05Had879W00Fm53quiJd3Zuz8h1JSNJ3nGSlbZ/7Tjs1tKyScgN3Au3t3MyPsjPlq60fMmSHLsg==}
    engines: {node: '>= 10'}
    cpu: [x64]
    os: [linux]

  '@next/swc-linux-x64-musl@15.5.19':
    resolution: {integrity: sha512-eoNQSpA5PQfB9wBO4RA47MTDXWz1fizy9Y3Z6e4DetYIF3dvjuu8sj7aIGn/bFCU6lnFzTK34NtCaffP4NsQ7Q==}
    engines: {node: '>= 10'}
    cpu: [x64]
    os: [linux]

  '@next/swc-win32-arm64-msvc@15.5.19':
    resolution: {integrity: sha512-6UNt2dFuCHOe446sm/Kp69nUe8/wIhnh9bm6Xcqw4qEWCOppLMOvhTBVgvM7invVUNr4SPpP6NOQsACtn2IN9Q==}
    engines: {node: '>= 10'}
    cpu: [arm64]
    os: [win32]

  '@next/swc-win32-x64-msvc@15.5.19':
    resolution: {integrity: sha512-PhmojAHyqMne56HBLGu9dhDnHPuFmEjrXSQMM/nW0J6j849lk3ESrVtqNJcCk8CKOV7brpTTbaYAjwKPzKM69w==}
    engines: {node: '>= 10'}
    cpu: [x64]
    os: [win32]

  '@nodelib/fs.scandir@2.1.5':
    resolution: {integrity: sha512-vq24Bq3ym5HEQm2NKCr3yXDwjc7vTsEThRDnkp2DK9p1uqLR+DHurm/NOTo0KG7HYHU7eppKZj3MyqYuMBf62g==}
    engines: {node: '>= 8'}

  '@nodelib/fs.stat@2.0.5':
    resolution: {integrity: sha512-RkhPPp2zrqDAQA/2jNhnztcPAlv64XdhIp7a7454A5ovI7Bukxgt7MX7udwAu3zg1DcpPU0rz3VV1SeaqvY4+A==}
    engines: {node: '>= 8'}

  '@nodelib/fs.walk@1.2.8':
    resolution: {integrity: sha512-oGB+UxlgWcgQkgwo8GcEGwemoTFt3FIO9ababBmaGwXIoBKZ+GTy0pP185beGg7Llih/NSHSV2XAs1lnznocSg==}
    engines: {node: '>= 8'}

  '@nolyfill/is-core-module@1.0.39':
    resolution: {integrity: sha512-nn5ozdjYQpUCZlWGuxcJY/KpxkWQs4DcbMCmKojjyrYDEAGy4Ce19NN4v5MduafTwJlbKc99UA8YhSVqq9yPZA==}
    engines: {node: '>=12.4.0'}

  '@playwright/test@1.60.0':
    resolution: {integrity: sha512-O71yZIbAh/PxDMNGns37GHBIfrVkEVyn+AXyIa5dOTfb4/xNvRWV+Vv/NMbNCtODB/pO7vLlF2OTmMVLhmr7Ag==}
    engines: {node: '>=18'}
    hasBin: true

  '@radix-ui/primitive@1.1.4':
    resolution: {integrity: sha512-7AdCK9PQyiljKoBDbN8OuctCbd/esdwZPQ8RtOE3SsyQtUpiPb+ND75q0jEhC1m1ecBI0MFNeLJvwIh9iKHRcQ==}

  '@radix-ui/react-collection@1.1.9':
    resolution: {integrity: sha512-zuSVi7ziP7uQRqc+yGxsKJfNkdyHv3ZKDaHe0gzg4dRgws96TPKWIiz84tVHP4GEcEl8bC0mdt17NkcxaJHmaQ==}
    peerDependencies:
      '@types/react': '*'
      '@types/react-dom': '*'
      react: ^16.8 || ^17.0 || ^18.0 || ^19.0 || ^19.0.0-rc
      react-dom: ^16.8 || ^17.0 || ^18.0 || ^19.0 || ^19.0.0-rc
    peerDependenciesMeta:
      '@types/react':
        optional: true
      '@types/react-dom':
        optional: true

  '@radix-ui/react-compose-refs@1.1.3':
    resolution: {integrity: sha512-rYOP8OMnuuPMQF1uhPVlGNcCDlkokKqGFE3JcxFViIkAXP7EvFWUliJAstrapypaBLJNHbZL6jGhbVDGTwmVhA==}
    peerDependencies:
      '@types/react': '*'
      react: ^16.8 || ^17.0 || ^18.0 || ^19.0 || ^19.0.0-rc
    peerDependenciesMeta:
      '@types/react':
        optional: true

  '@radix-ui/react-context@1.1.4':
    resolution: {integrity: sha512-QwH4PO5urrbO+FaGd5Aglg+YJgWTyyuZ3g/6mKvsqraLkglDdckw9JafgL5McL5VEJ6EPNduPaT3ZE9BttDAqg==}
    peerDependencies:
      '@types/react': '*'
      react: ^16.8 || ^17.0 || ^18.0 || ^19.0 || ^19.0.0-rc
    peerDependenciesMeta:
      '@types/react':
        optional: true

  '@radix-ui/react-dialog@1.1.16':
    resolution: {integrity: sha512-l9ok83YBclEZhbjgzt76Hw733e6cvRKPNgO6GJ/IETlufXG9p+fRu2wlvpImQvR6xdJ8h7J8J2DBvsPEiEsKMw==}
    peerDependencies:
      '@types/react': '*'
      '@types/react-dom': '*'
      react: ^16.8 || ^17.0 || ^18.0 || ^19.0 || ^19.0.0-rc
      react-dom: ^16.8 || ^17.0 || ^18.0 || ^19.0 || ^19.0.0-rc
    peerDependenciesMeta:
      '@types/react':
        optional: true
      '@types/react-dom':
        optional: true

  '@radix-ui/react-direction@1.1.2':
    resolution: {integrity: sha512-C3vFhbyi4SW3PmbAi6Awpu4OzJtd0MxGurvSsYtr7p7nM8RNB3VAF3CUmnp2j50knpkrRcB7+ycVXzgLgF6yNA==}
    peerDependencies:
      '@types/react': '*'
      react: ^16.8 || ^17.0 || ^18.0 || ^19.0 || ^19.0.0-rc
    peerDependenciesMeta:
      '@types/react':
        optional: true

  '@radix-ui/react-dismissable-layer@1.1.12':
    resolution: {integrity: sha512-MhoruH6xEzsbvOmo4TNgMfmtvRGyDZw4MDSdf4ybMHfezjqwzv6hyd4lsMzBp8K9Sn6sGzCF62x1I7BYUECXOg==}
    peerDependencies:
      '@types/react': '*'
      '@types/react-dom': '*'
      react: ^16.8 || ^17.0 || ^18.0 || ^19.0 || ^19.0.0-rc
      react-dom: ^16.8 || ^17.0 || ^18.0 || ^19.0 || ^19.0.0-rc
    peerDependenciesMeta:
      '@types/react':
        optional: true
      '@types/react-dom':
        optional: true

  '@radix-ui/react-focus-guards@1.1.4':
    resolution: {integrity: sha512-cot/aB/mOm0IYVYTTmQcEEK1M48lZWi8FlYe5nDPQQ8NYZUlXEFgncJ9p2Kzer3RKSrY7cTTpEMLZKNo9QoP5Q==}
    peerDependencies:
      '@types/react': '*'
      react: ^16.8 || ^17.0 || ^18.0 || ^19.0 || ^19.0.0-rc
    peerDependenciesMeta:
      '@types/react':
        optional: true

  '@radix-ui/react-focus-scope@1.1.9':
    resolution: {integrity: sha512-9Se8t+Zry+1rEOL7Y6l/4ANYU/TOtAtf8O2fKdwLltcaMcm6kOqYGbzO4tMFQ0bvzO920pRAoHpFZ4W85S3keQ==}
    peerDependencies:
      '@types/react': '*'
      '@types/react-dom': '*'
      react: ^16.8 || ^17.0 || ^18.0 || ^19.0 || ^19.0.0-rc
      react-dom: ^16.8 || ^17.0 || ^18.0 || ^19.0 || ^19.0.0-rc
    peerDependenciesMeta:
      '@types/react':
        optional: true
      '@types/react-dom':
        optional: true

  '@radix-ui/react-id@1.1.2':
    resolution: {integrity: sha512-orBC88futVpqCmhX1p4cvquNHsELQ+w+vBJnuj3ftETI5bJb0bZn3Tqu3SWN2IOcPycTnMGnhwoermvISt72sA==}
    peerDependencies:
      '@types/react': '*'
      react: ^16.8 || ^17.0 || ^18.0 || ^19.0 || ^19.0.0-rc
    peerDependenciesMeta:
      '@types/react':
        optional: true

  '@radix-ui/react-portal@1.1.11':
    resolution: {integrity: sha512-UEytdjgEh2tJGgD/gZK4FUx6t1rNIlM3U0DENhSrG7I75FGm1DnaDuVUWF1pWAWUwGmn1sCJ1VGHn8LhN1aTOw==}
    peerDependencies:
      '@types/react': '*'
      '@types/react-dom': '*'
      react: ^16.8 || ^17.0 || ^18.0 || ^19.0 || ^19.0.0-rc
      react-dom: ^16.8 || ^17.0 || ^18.0 || ^19.0 || ^19.0.0-rc
    peerDependenciesMeta:
      '@types/react':
        optional: true
      '@types/react-dom':
        optional: true

  '@radix-ui/react-presence@1.1.6':
    resolution: {integrity: sha512-zdTk4PlUO0E18HnZ3wYbW0KkJJxWCdiNYp6g6X1PtONFhxVkg01vliTJAmwIszU6mHiyBOoW9P0rAugl5/hULQ==}
    peerDependencies:
      '@types/react': '*'
      '@types/react-dom': '*'
      react: ^16.8 || ^17.0 || ^18.0 || ^19.0 || ^19.0.0-rc
      react-dom: ^16.8 || ^17.0 || ^18.0 || ^19.0 || ^19.0.0-rc
    peerDependenciesMeta:
      '@types/react':
        optional: true
      '@types/react-dom':
        optional: true

  '@radix-ui/react-primitive@2.1.5':
    resolution: {integrity: sha512-zifXeB8Y88qCYx8PLZ5oQb32KwZub+s925mMoZsBBq9KUQqWKkREubTfs6ASjRPPBe7Jt9O8OHH89+95VG+grA==}
    peerDependencies:
      '@types/react': '*'
      '@types/react-dom': '*'
      react: ^16.8 || ^17.0 || ^18.0 || ^19.0 || ^19.0.0-rc
      react-dom: ^16.8 || ^17.0 || ^18.0 || ^19.0 || ^19.0.0-rc
    peerDependenciesMeta:
      '@types/react':
        optional: true
      '@types/react-dom':
        optional: true

  '@radix-ui/react-roving-focus@1.1.12':
    resolution: {integrity: sha512-FvgPt1bRmg8Xt2QpF7NUZW3dE0ZQHGm41dAdgT2J2GJPoIXz+9Em3NobAxf4fupcxhgHu03E5CRiU2MWvObXyg==}
    peerDependencies:
      '@types/react': '*'
      '@types/react-dom': '*'
      react: ^16.8 || ^17.0 || ^18.0 || ^19.0 || ^19.0.0-rc
      react-dom: ^16.8 || ^17.0 || ^18.0 || ^19.0 || ^19.0.0-rc
    peerDependenciesMeta:
      '@types/react':
        optional: true
      '@types/react-dom':
        optional: true

  '@radix-ui/react-slot@1.2.5':
    resolution: {integrity: sha512-rCMO3QsIVKv5JTY5CVbo2MvO77SpEqqYc8AvRE7OWqRDOIqAKjsp+DrmnY9uc8NPdxB5E2z47HTYGeE2+NTptg==}
    peerDependencies:
      '@types/react': '*'
      react: ^16.8 || ^17.0 || ^18.0 || ^19.0 || ^19.0.0-rc
    peerDependenciesMeta:
      '@types/react':
        optional: true

  '@radix-ui/react-tabs@1.1.14':
    resolution: {integrity: sha512-D5jwp9JNuwDeCw3CYD2Fz+sSHo0droQjC8u75dJHe4aWr5q6yBiXZU+hurXnKudRgEpUkD5TsI6bjHPo5ThUxA==}
    peerDependencies:
      '@types/react': '*'
      '@types/react-dom': '*'
      react: ^16.8 || ^17.0 || ^18.0 || ^19.0 || ^19.0.0-rc
      react-dom: ^16.8 || ^17.0 || ^18.0 || ^19.0 || ^19.0.0-rc
    peerDependenciesMeta:
      '@types/react':
        optional: true
      '@types/react-dom':
        optional: true

  '@radix-ui/react-use-callback-ref@1.1.2':
    resolution: {integrity: sha512-xCso9j1/u8sEgP1RNHjFrXJLApL8LiqOkI1R4ywuN00rxWdYg4oQXuwKLS3i0j5NWLromUD27/4nlxj2UFVvIw==}
    peerDependencies:
      '@types/react': '*'
      react: ^16.8 || ^17.0 || ^18.0 || ^19.0 || ^19.0.0-rc
    peerDependenciesMeta:
      '@types/react':
        optional: true

  '@radix-ui/react-use-controllable-state@1.2.3':
    resolution: {integrity: sha512-PLzC90MS+ReootmjC597dvopoelpZ8Q61HJkDXZSExitIq7PL55vHNnesAHwguHK0aPfBnpdNzQtv1uliaqQrA==}
    peerDependencies:
      '@types/react': '*'
      react: ^16.8 || ^17.0 || ^18.0 || ^19.0 || ^19.0.0-rc
    peerDependenciesMeta:
      '@types/react':
        optional: true

  '@radix-ui/react-use-effect-event@0.0.3':
    resolution: {integrity: sha512-6c8ZqvPTWILEKnyVkP53EGRCcpnJiKTC21sS/6R1GF5xKyHJJWQEPfkqlcgUkdRQivd6tb23abUwe4ngWmY0JA==}
    peerDependencies:
      '@types/react': '*'
      react: ^16.8 || ^17.0 || ^18.0 || ^19.0 || ^19.0.0-rc
    peerDependenciesMeta:
      '@types/react':
        optional: true

  '@radix-ui/react-use-escape-keydown@1.1.2':
    resolution: {integrity: sha512-2uVLvLjgO7NZCWw01/FdqRwmA42J0BcjPMUCA+koFEOAb+zjqIP7SiFz/7zWPrKnVmSqr76Omq2ALyCuX4dhLw==}
    peerDependencies:
      '@types/react': '*'
      react: ^16.8 || ^17.0 || ^18.0 || ^19.0 || ^19.0.0-rc
    peerDependenciesMeta:
      '@types/react':
        optional: true

  '@radix-ui/react-use-layout-effect@1.1.2':
    resolution: {integrity: sha512-jrBWOxZITuGcnjRCM2t2U5ZPkCLxD+Ym6DjfssS5haTj2iiak/DOb64JeN6OdLfLgptb6/e2kKR+ZuTrGoZTPA==}
    peerDependencies:
      '@types/react': '*'
      react: ^16.8 || ^17.0 || ^18.0 || ^19.0 || ^19.0.0-rc
    peerDependenciesMeta:
      '@types/react':
        optional: true

  '@react-native-async-storage/async-storage@2.2.0':
    resolution: {integrity: sha512-gvRvjR5JAaUZF8tv2Kcq/Gbt3JHwbKFYfmb445rhOj6NUMx3qPLixmDx5pZAyb9at1bYvJ4/eTUipU5aki45xw==}
    peerDependencies:
      react-native: ^0.0.0-0 || >=0.65 <1.0

  '@react-native-masked-view/masked-view@0.3.2':
    resolution: {integrity: sha512-XwuQoW7/GEgWRMovOQtX3A4PrXhyaZm0lVUiY8qJDvdngjLms9Cpdck6SmGAUNqQwcj2EadHC1HwL0bEyoa/SQ==}
    peerDependencies:
      react: '>=16'
      react-native: '>=0.57'

  '@react-native/assets-registry@0.81.5':
    resolution: {integrity: sha512-705B6x/5Kxm1RKRvSv0ADYWm5JOnoiQ1ufW7h8uu2E6G9Of/eE6hP/Ivw3U5jI16ERqZxiKQwk34VJbB0niX9w==}
    engines: {node: '>= 20.19.4'}

  '@react-native/babel-plugin-codegen@0.81.5':
    resolution: {integrity: sha512-oF71cIH6je3fSLi6VPjjC3Sgyyn57JLHXs+mHWc9MoCiJJcM4nqsS5J38zv1XQ8d3zOW2JtHro+LF0tagj2bfQ==}
    engines: {node: '>= 20.19.4'}

  '@react-native/babel-plugin-codegen@0.85.3':
    resolution: {integrity: sha512-Wc94zGfeFG8Njf9SHMPfYZP04kjigkOps6F1TYTvd7ZVXuGxqseCDgxc50LWcOhOCLypI9n3oVVqz81C3p44ZA==}
    engines: {node: ^20.19.4 || ^22.13.0 || ^24.3.0 || >= 25.0.0}

  '@react-native/babel-preset@0.81.5':
    resolution: {integrity: sha512-UoI/x/5tCmi+pZ3c1+Ypr1DaRMDLI3y+Q70pVLLVgrnC3DHsHRIbHcCHIeG/IJvoeFqFM2sTdhSOLJrf8lOPrA==}
    engines: {node: '>= 20.19.4'}
    peerDependencies:
      '@babel/core': '*'

  '@react-native/babel-preset@0.85.3':
    resolution: {integrity: sha512-fD7fxEhkJB/aF57tWoXjaAWpklfrExYZS3k6aXPP3BQ77DZY7gvf/b7dbirwjID6NVnP1JDRJyTuPBGr0K/vlw==}
    engines: {node: ^20.19.4 || ^22.13.0 || ^24.3.0 || >= 25.0.0}
    peerDependencies:
      '@babel/core': '*'

  '@react-native/codegen@0.81.5':
    resolution: {integrity: sha512-a2TDA03Up8lpSa9sh5VRGCQDXgCTOyDOFH+aqyinxp1HChG8uk89/G+nkJ9FPd0rqgi25eCTR16TWdS3b+fA6g==}
    engines: {node: '>= 20.19.4'}
    peerDependencies:
      '@babel/core': '*'

  '@react-native/codegen@0.85.3':
    resolution: {integrity: sha512-/JkS1lGLyzBWP1FbgDwaqEf7qShIC6pUC1M0a/YMAd/v4iqR24MRkQWe7jkYvcBQ2LpEhs5NGE9InhxSv21zCA==}
    engines: {node: ^20.19.4 || ^22.13.0 || ^24.3.0 || >= 25.0.0}
    peerDependencies:
      '@babel/core': '*'

  '@react-native/community-cli-plugin@0.81.5':
    resolution: {integrity: sha512-yWRlmEOtcyvSZ4+OvqPabt+NS36vg0K/WADTQLhrYrm9qdZSuXmq8PmdJWz/68wAqKQ+4KTILiq2kjRQwnyhQw==}
    engines: {node: '>= 20.19.4'}
    peerDependencies:
      '@react-native-community/cli': '*'
      '@react-native/metro-config': '*'
    peerDependenciesMeta:
      '@react-native-community/cli':
        optional: true
      '@react-native/metro-config':
        optional: true

  '@react-native/debugger-frontend@0.81.5':
    resolution: {integrity: sha512-bnd9FSdWKx2ncklOetCgrlwqSGhMHP2zOxObJbOWXoj7GHEmih4MKarBo5/a8gX8EfA1EwRATdfNBQ81DY+h+w==}
    engines: {node: '>= 20.19.4'}

  '@react-native/dev-middleware@0.81.5':
    resolution: {integrity: sha512-WfPfZzboYgo/TUtysuD5xyANzzfka8Ebni6RIb2wDxhb56ERi7qDrE4xGhtPsjCL4pQBXSVxyIlCy0d8I6EgGA==}
    engines: {node: '>= 20.19.4'}

  '@react-native/gradle-plugin@0.81.5':
    resolution: {integrity: sha512-hORRlNBj+ReNMLo9jme3yQ6JQf4GZpVEBLxmTXGGlIL78MAezDZr5/uq9dwElSbcGmLEgeiax6e174Fie6qPLg==}
    engines: {node: '>= 20.19.4'}

  '@react-native/js-polyfills@0.81.5':
    resolution: {integrity: sha512-fB7M1CMOCIUudTRuj7kzxIBTVw2KXnsgbQ6+4cbqSxo8NmRRhA0Ul4ZUzZj3rFd3VznTL4Brmocv1oiN0bWZ8w==}
    engines: {node: '>= 20.19.4'}

  '@react-native/js-polyfills@0.85.3':
    resolution: {integrity: sha512-U2+aMshIXf1uFn77tpBb/xhHWB9vkVrMpt7kkucAugF8hJKYTDGB587X7WwelHduK2KBfhl4giSv0rzZGoef9A==}
    engines: {node: ^20.19.4 || ^22.13.0 || ^24.3.0 || >= 25.0.0}

  '@react-native/metro-babel-transformer@0.85.3':
    resolution: {integrity: sha512-omuKq+r7jM4XvCMIlNMPP7Up3SyB8o5EAdZtF7YXniKyq7UOMBqhYHFqgsdOXr0lT+3ADf7VCJG3sb82jlBrrQ==}
    engines: {node: ^20.19.4 || ^22.13.0 || ^24.3.0 || >= 25.0.0}
    peerDependencies:
      '@babel/core': '*'

  '@react-native/metro-config@0.85.3':
    resolution: {integrity: sha512-sVo6HepUmCcpdfozEf91lA0FjpLNNZYu/Zi9FiYiAQTK8pzATXDVTqhvdxpFrQn435p5eUTSbllvbH/KN+bnyA==}
    engines: {node: ^20.19.4 || ^22.13.0 || ^24.3.0 || >= 25.0.0}

  '@react-native/normalize-colors@0.74.89':
    resolution: {integrity: sha512-qoMMXddVKVhZ8PA1AbUCk83trpd6N+1nF2A6k1i6LsQObyS92fELuk8kU/lQs6M7BsMHwqyLCpQJ1uFgNvIQXg==}

  '@react-native/normalize-colors@0.81.5':
    resolution: {integrity: sha512-0HuJ8YtqlTVRXGZuGeBejLE04wSQsibpTI+RGOyVqxZvgtlLLC/Ssw0UmbHhT4lYMp2fhdtvKZSs5emWB1zR/g==}

  '@react-native/virtualized-lists@0.81.5':
    resolution: {integrity: sha512-UVXgV/db25OPIvwZySeToXD/9sKKhOdkcWmmf4Jh8iBZuyfML+/5CasaZ1E7Lqg6g3uqVQq75NqIwkYmORJMPw==}
    engines: {node: '>= 20.19.4'}
    peerDependencies:
      '@types/react': ^19.1.0
      react: '*'
      react-native: '*'
    peerDependenciesMeta:
      '@types/react':
        optional: true

  '@react-navigation/core@6.4.17':
    resolution: {integrity: sha512-Nd76EpomzChWAosGqWOYE3ItayhDzIEzzZsT7PfGcRFDgW5miHV2t4MZcq9YIK4tzxZjVVpYbIynOOQQd1e0Cg==}
    deprecated: This version is no longer supported
    peerDependencies:
      react: '*'

  '@react-navigation/elements@1.3.31':
    resolution: {integrity: sha512-bUzP4Awlljx5RKEExw8WYtif8EuQni2glDaieYROKTnaxsu9kEIA515sXQgUDZU4Ob12VoL7+z70uO3qrlfXcQ==}
    deprecated: This version is no longer supported
    peerDependencies:
      '@react-navigation/native': ^6.0.0
      react: '*'
      react-native: '*'
      react-native-safe-area-context: '>= 3.0.0'

  '@react-navigation/native-stack@6.11.0':
    resolution: {integrity: sha512-U5EcUB9Q2NQspCFwYGGNJm0h6wBCOv7T30QjndmvlawLkNt7S7KWbpWyxS9XBHSIKF57RgWjfxuJNTgTstpXxw==}
    peerDependencies:
      '@react-navigation/native': ^6.0.0
      react: '*'
      react-native: '*'
      react-native-safe-area-context: '>= 3.0.0'
      react-native-screens: '>= 3.0.0'

  '@react-navigation/native@6.1.18':
    resolution: {integrity: sha512-mIT9MiL/vMm4eirLcmw2h6h/Nm5FICtnYSdohq4vTLA2FF/6PNhByM7s8ffqoVfE5L0uAa6Xda1B7oddolUiGg==}
    deprecated: This version is no longer supported
    peerDependencies:
      react: '*'
      react-native: '*'

  '@react-navigation/routers@6.1.9':
    resolution: {integrity: sha512-lTM8gSFHSfkJvQkxacGM6VJtBt61ip2XO54aNfswD+KMw6eeZ4oehl7m0me3CR9hnDE4+60iAZR8sAhvCiI3NA==}
    deprecated: This version is no longer supported

  '@rtsao/scc@1.1.0':
    resolution: {integrity: sha512-zt6OdqaDoOnJ1ZYsCYGt9YmWzDXl4vQdKTyJev62gFhRGKdx7mcT54V9KIjg+d2wi9EXsPvAPKe7i7WjfVWB8g==}

  '@sinclair/typebox@0.27.10':
    resolution: {integrity: sha512-MTBk/3jGLNB2tVxv6uLlFh1iu64iYOQ2PbdOSK3NW8JZsmlaOh2q6sdtKowBhfw8QFLmYNzTW4/oK4uATIi6ZA==}

  '@sinonjs/commons@3.0.1':
    resolution: {integrity: sha512-K3mCHKQ9sVh8o1C9cxkwxaOmXoAMlDxC1mYyHrjqOWEcBjYr76t96zL2zlj5dUGZ3HSw240X1qgH3Mjf1yJWpQ==}

  '@sinonjs/fake-timers@10.3.0':
    resolution: {integrity: sha512-V4BG07kuYSUkTCSBHG8G8TNhM+F19jXFWnQtzj+we8DrkpSBCee9Z3Ms8yiGer/dlmhe35/Xdgyo3/0rQKg7YA==}

  '@swc/helpers@0.5.15':
    resolution: {integrity: sha512-JQ5TuMi45Owi4/BIMAJBoSQoOJu12oOk/gADqlcUL9JEdHB8vyjUSsxqeNXnmXHjYKMi2WcYtezGEEhqUI/E2g==}

  '@tanstack/query-core@5.101.0':
    resolution: {integrity: sha512-cQetA74EB+seWySv1TTKr828TnP0u39m6LykwDXIo84SNortpDkp30TMEjkqtYCNP9c40uT/iwl6MLiufEt0Ow==}

  '@tanstack/react-query@5.101.0':
    resolution: {integrity: sha512-rLlJXSpkqfizLWgkR5+eLeIk0MvTx/meEIR7LRjxic+qxiQP8zVjq7BqQkiCMNLQBlLfuOLqqr6KO5GtrDlmSg==}
    peerDependencies:
      react: ^18 || ^19

  '@testing-library/dom@10.4.1':
    resolution: {integrity: sha512-o4PXJQidqJl82ckFaXUeoAW+XysPLauYI43Abki5hABd853iMhitooc6znOnczgbTYmEP6U6/y1ZyKAIsvMKGg==}
    engines: {node: '>=18'}

  '@testing-library/jest-dom@6.9.1':
    resolution: {integrity: sha512-zIcONa+hVtVSSep9UT3jZ5rizo2BsxgyDYU7WFD5eICBE7no3881HGeb/QkGfsJs6JTkY1aQhT7rIPC7e+0nnA==}
    engines: {node: '>=14', npm: '>=6', yarn: '>=1'}

  '@testing-library/react-native@12.9.0':
    resolution: {integrity: sha512-wIn/lB1FjV2N4Q7i9PWVRck3Ehwq5pkhAef5X5/bmQ78J/NoOsGbVY2/DG5Y9Lxw+RfE+GvSEh/fe5Tz6sKSvw==}
    deprecated: React Native Testing Library v12 is no longer maintained. Please upgrade to v13 or v14.
    peerDependencies:
      jest: '>=28.0.0'
      react: '>=16.8.0'
      react-native: '>=0.59'
      react-test-renderer: '>=16.8.0'
    peerDependenciesMeta:
      jest:
        optional: true

  '@testing-library/user-event@14.6.1':
    resolution: {integrity: sha512-vq7fv0rnt+QTXgPxr5Hjc210p6YKq2kmdziLgnsZGgLJ9e6VAShx1pACLuRjd/AS/sr7phAR58OIIpf0LlmQNw==}
    engines: {node: '>=12', npm: '>=6'}
    peerDependencies:
      '@testing-library/dom': '>=7.21.4'

  '@turbo/darwin-64@2.9.16':
    resolution: {integrity: sha512-jLjApWTSNd7JZ5JaLYfelW1ytnGQOvB7ivl+2RD1xQvJTbi8I9gBjzcga7tDZVPyaxpl10YTfJt3BrYXR18KDw==}
    cpu: [x64]
    os: [darwin]

  '@turbo/darwin-arm64@2.9.16':
    resolution: {integrity: sha512-YPgrn+5HIGzrx0O2a631SV4MBQUe4W/DafMFUuBVgaU32PW9/OTT0ehviF0QSxTXuRJlHvW2eUTemddF5/spmw==}
    cpu: [arm64]
    os: [darwin]

  '@turbo/linux-64@2.9.16':
    resolution: {integrity: sha512-vAEf1H6l26lTpl9FJ/peQo1NUB8RC0sbEJJz5mPcUhHA2bPDup2x3CZPgo/bH8S4cUcBLm4FN3UHd5iUO2RAew==}
    cpu: [x64]
    os: [linux]

  '@turbo/linux-arm64@2.9.16':
    resolution: {integrity: sha512-xDBLR2PZg4BrQOchfG6svgpv5FCNJ2TOtT2psLdEJcdKo1BH+pnPs9Xj6pvUjgfkHbuvBOfeE4R6tvxMoQKDHQ==}
    cpu: [arm64]
    os: [linux]

  '@turbo/windows-64@2.9.16':
    resolution: {integrity: sha512-NBAJnaUiGdgkSzQwUIdOvkCkcpTSu58G/sBGa0mvBtzfvFOOgrQwepKOOQ8cp6sWM6OcKDNFj2p1dsZA1OWjPg==}
    cpu: [x64]
    os: [win32]

  '@turbo/windows-arm64@2.9.16':
    resolution: {integrity: sha512-Y7SJppD0Z8wjO3Ec0ZGd9KQ4Yv0BMnA8CIowj5Vp+OEVsosXDG2weK6/t1RRLfJmc2Ozrnd6y4DOgQys+mn3WQ==}
    cpu: [arm64]
    os: [win32]

  '@tybys/wasm-util@0.10.2':
    resolution: {integrity: sha512-RoBvJ2X0wuKlWFIjrwffGw1IqZHKQqzIchKaadZZfnNpsAYp2mM0h36JtPCjNDAHGgYez/15uMBpfGwchhiMgg==}

  '@types/aria-query@5.0.4':
    resolution: {integrity: sha512-rfT93uj5s0PRL7EzccGMs3brplhcrghnDoV26NqKhCAS1hVo+WdNsPvE/yb6ilfr5hi2MEk6d5EWJTKdxg8jVw==}

  '@types/babel__core@7.20.5':
    resolution: {integrity: sha512-qoQprZvz5wQFJwMDqeseRXWv3rqMvhgpbXFfVyWhbx9X47POIA6i/+dXefEmZKoAgOaTdaIgNSMqMIU61yRyzA==}

  '@types/babel__generator@7.27.0':
    resolution: {integrity: sha512-ufFd2Xi92OAVPYsy+P4n7/U7e68fex0+Ee8gSG9KX7eo084CWiQ4sdxktvdl0bOPupXtVJPY19zk6EwWqUQ8lg==}

  '@types/babel__template@7.4.4':
    resolution: {integrity: sha512-h/NUaSyG5EyxBIp8YRxo4RMe2/qQgvyowRwVMzhYhBCONbW8PUsg4lkFMrhgZhUe5z3L3MiLDuvyJ/CaPa2A8A==}

  '@types/babel__traverse@7.28.0':
    resolution: {integrity: sha512-8PvcXf70gTDZBgt9ptxJ8elBeBjcLOAcOtoO/mPJjtji1+CdGbHgm77om1GrsPxsiE+uXIpNSK64UYaIwQXd4Q==}

  '@types/graceful-fs@4.1.9':
    resolution: {integrity: sha512-olP3sd1qOEe5dXTSaFvQG+02VdRXcdytWLAZsAq1PecU8uqQAhkrnbli7DagjtXKW/Bl7YJbUsa8MPcuc8LHEQ==}

  '@types/istanbul-lib-coverage@2.0.6':
    resolution: {integrity: sha512-2QF/t/auWm0lsy8XtKVPG19v3sSOQlJe/YHZgfjb/KBBHOGSV+J2q/S671rcq9uTBrLAXmZpqJiaQbMT+zNU1w==}

  '@types/istanbul-lib-report@3.0.3':
    resolution: {integrity: sha512-NQn7AHQnk/RSLOxrBbGyJM/aVQ+pjj5HCgasFxc0K/KhoATfQ/47AyUl15I2yBUpihjmas+a+VJBOqecrFH+uA==}

  '@types/istanbul-reports@3.0.4':
    resolution: {integrity: sha512-pk2B1NWalF9toCRu6gjBzR69syFjP4Od8WRAX+0mmf9lAjCRicLOWc+ZrxZHx/0XRjotgkF9t6iaMJ+aXcOdZQ==}

  '@types/json5@0.0.29':
    resolution: {integrity: sha512-dRLjCWHYg4oaA77cxO64oO+7JwCwnIzkZPdrrC71jQmQtlhM556pwKo5bUzqvZndkVbeFLIIi+9TC40JNF5hNQ==}

  '@types/node@22.19.20':
    resolution: {integrity: sha512-6tELRwSDYWW9EdZhbeZmYGZ1/7Djkt+Ah3/ScEYT9cDord7UJzasR/4D3VONg9tQI5CDp+/CZC1AXj2pCFOvpw==}

  '@types/react-dom@19.2.3':
    resolution: {integrity: sha512-jp2L/eY6fn+KgVVQAOqYItbF0VY/YApe5Mz2F0aykSO8gx31bYCZyvSeYxCHKvzHG5eZjc+zyaS5BrBWya2+kQ==}
    peerDependencies:
      '@types/react': ^19.2.0

  '@types/react-native@0.73.0':
    resolution: {integrity: sha512-6ZRPQrYM72qYKGWidEttRe6M5DZBEV5F+MHMHqd4TTYx0tfkcdrUFGdef6CCxY0jXU7wldvd/zA/b0A/kTeJmA==}
    deprecated: This is a stub types definition. react-native provides its own type definitions, so you do not need this installed.

  '@types/react-navigation@3.4.0':
    resolution: {integrity: sha512-Y7F5zU8BTBK8tEOvUqgvwvPZ7+9vnc2UI1vHwJ/9ZJG98TntNv04GWa6lrn4MA4149pqw6cyNw/V49Yd2osAFQ==}
    deprecated: This is a stub types definition. react-navigation provides its own type definitions, so you do not need this installed.

  '@types/react-test-renderer@19.1.0':
    resolution: {integrity: sha512-XD0WZrHqjNrxA/MaR9O22w/RNidWR9YZmBdRGI7wcnWGrv/3dA8wKCJ8m63Sn+tLJhcjmuhOi629N66W6kgWzQ==}

  '@types/react@19.1.17':
    resolution: {integrity: sha512-Qec1E3mhALmaspIrhWt9jkQMNdw6bReVu64mjvhbhq2NFPftLPVr+l1SZgmw/66WwBNpDh7ao5AT6gF5v41PFA==}

  '@types/stack-utils@2.0.3':
    resolution: {integrity: sha512-9aEbYZ3TbYMznPdcdr3SmIrLXwC/AKZXQeCf9Pgao5CKb8CyHuEX5jzWPTkvregvhRJHcpRO6BFoGW9ycaOkYw==}

  '@types/yargs-parser@21.0.3':
    resolution: {integrity: sha512-I4q9QU9MQv4oEOz4tAHJtNz1cwuLxn2F3xcc2iV5WdqLPpUnj30aUuxt1mAxYTG+oe8CZMV/+6rU4S4gRDzqtQ==}

  '@types/yargs@17.0.35':
    resolution: {integrity: sha512-qUHkeCyQFxMXg79wQfTtfndEC+N9ZZg76HJftDJp+qH2tV7Gj4OJi7l+PiWwJ+pWtW8GwSmqsDj/oymhrTWXjg==}

  '@typescript-eslint/eslint-plugin@8.60.1':
    resolution: {integrity: sha512-JQ4S5GB0tfjO8BuJ4fcX+HodkzJjYBV+7OJ+wLygaX7OGQ7FudyHL4NSCA6ob+w3Yn+5MkKIozOwQhXeM7opVg==}
    engines: {node: ^18.18.0 || ^20.9.0 || >=21.1.0}
    peerDependencies:
      '@typescript-eslint/parser': ^8.60.1
      eslint: ^8.57.0 || ^9.0.0 || ^10.0.0
      typescript: '>=4.8.4 <6.1.0'

  '@typescript-eslint/parser@8.60.1':
    resolution: {integrity: sha512-A0M6ua6H252bVjPvvtSgl2QA4+ET9S5Mtkb2GDyTxIhH/C4qDItT7RQNO5PhMC6NXGYXOR9dIalcDDgBKT7oFA==}
    engines: {node: ^18.18.0 || ^20.9.0 || >=21.1.0}
    peerDependencies:
      eslint: ^8.57.0 || ^9.0.0 || ^10.0.0
      typescript: '>=4.8.4 <6.1.0'

  '@typescript-eslint/project-service@8.60.1':
    resolution: {integrity: sha512-eXkTH2bxmXlqD1RnOPmLZ9ZM9D3VwSx04JOwBnP9RQ+yUA5a2Mu7SfW8uaV2Aon53NJzZlZYuX7tn91Izf+xaw==}
    engines: {node: ^18.18.0 || ^20.9.0 || >=21.1.0}
    peerDependencies:
      typescript: '>=4.8.4 <6.1.0'

  '@typescript-eslint/scope-manager@8.60.1':
    resolution: {integrity: sha512-gvI5OQoptnxQnchOirukCuQ55svJSTuD/4k5+pC267xyBtYry748R9/c3tYUzb/iE6RZfllRz2lVulLCHkTm4w==}
    engines: {node: ^18.18.0 || ^20.9.0 || >=21.1.0}

  '@typescript-eslint/tsconfig-utils@8.60.1':
    resolution: {integrity: sha512-nh8w4qAteiKuZu3pSSzG/yGKpw0OlkrKnzFmbVRenKaD4qc+7i1GrmZaLVkr8rk4uipiPGMOW4YsM6WmKZ5CvA==}
    engines: {node: ^18.18.0 || ^20.9.0 || >=21.1.0}
    peerDependencies:
      typescript: '>=4.8.4 <6.1.0'

  '@typescript-eslint/type-utils@8.60.1':
    resolution: {integrity: sha512-sdwTrpjosW7ANQYJ39ZBF1ZyEMEGVB2UsikrserVM/30a/F1dTLnu9bGxEdosugyu5caigjLrR2qiD11asjI1A==}
    engines: {node: ^18.18.0 || ^20.9.0 || >=21.1.0}
    peerDependencies:
      eslint: ^8.57.0 || ^9.0.0 || ^10.0.0
      typescript: '>=4.8.4 <6.1.0'

  '@typescript-eslint/types@8.60.1':
    resolution: {integrity: sha512-4h0tY8ppCkdCzcrl2YM5M3my0xsE1Tf8om3owEu5oPWmXwkKRmk0j0LGDzYBGUcAlesEbxBhazqu/K4cu3Ug7w==}
    engines: {node: ^18.18.0 || ^20.9.0 || >=21.1.0}

  '@typescript-eslint/typescript-estree@8.60.1':
    resolution: {integrity: sha512-alpRkfG8hlVE5kdJW2GkfgDgXxold3e8e4l6EnmhRmRLbekgAPCCGDVD++sABy9FcgPFroq+uFcCSM1vR57Cew==}
    engines: {node: ^18.18.0 || ^20.9.0 || >=21.1.0}
    peerDependencies:
      typescript: '>=4.8.4 <6.1.0'

  '@typescript-eslint/utils@8.60.1':
    resolution: {integrity: sha512-h2MPBLoNtjc3qZWfY3Tl51yPorQ2McHn8pJfcMNTcIvrrZrr90Ykffit0yjrPFWQcRcUxzH20+6OcVdW4yHtUg==}
    engines: {node: ^18.18.0 || ^20.9.0 || >=21.1.0}
    peerDependencies:
      eslint: ^8.57.0 || ^9.0.0 || ^10.0.0
      typescript: '>=4.8.4 <6.1.0'

  '@typescript-eslint/visitor-keys@8.60.1':
    resolution: {integrity: sha512-EbGRQg4FhrmwLodl+t3JNAnXHWVr9Vp+Zl1QBZVPY4ByfkzIT8cX3K6QWODHtkIZqqJVEWvhHSx3v5PDHsaQag==}
    engines: {node: ^18.18.0 || ^20.9.0 || >=21.1.0}

  '@ungap/structured-clone@1.3.1':
    resolution: {integrity: sha512-mUFwbeTqrVgDQxFveS+df2yfap6iuP20NAKAsBt5jDEoOTDew+zwLAOilHCeQJOVSvmgCX4ogqIrA0mnyr08yQ==}

  '@unrs/resolver-binding-android-arm-eabi@1.12.2':
    resolution: {integrity: sha512-g5T90pqg1bo/7mytQx6F4iBNC0Wsh9cu+z9veDbFjc7HjpesJFWD7QMS0NGStXM075+7dJPPVvBbpZlnrdpi/w==}
    cpu: [arm]
    os: [android]

  '@unrs/resolver-binding-android-arm64@1.12.2':
    resolution: {integrity: sha512-YGCRZv/9GLhwmz6mYDeTsm/92BAyR28l6c2ReweVW5pWgfsitWLY8upvfRlGdoyD8HjeTHSYJWyZGD4KJA/nFQ==}
    cpu: [arm64]
    os: [android]

  '@unrs/resolver-binding-darwin-arm64@1.12.2':
    resolution: {integrity: sha512-u9DiNT1auQMO20A9SyTuG3wUgQWB9Z7KjAg0uFuCDR1FsAY8A0CG2S6JpHS1xwm/w1G08bjXZDcyOCjv1WAm2w==}
    cpu: [arm64]
    os: [darwin]

  '@unrs/resolver-binding-darwin-x64@1.12.2':
    resolution: {integrity: sha512-f7rPLi/T1HVKZu/u6t87lroib16n8vrSzcyxI7lg4BGO9UF26KhQL44sd9eOUgrTYhvRXtWOIZT5PejdPyJfUA==}
    cpu: [x64]
    os: [darwin]

  '@unrs/resolver-binding-freebsd-x64@1.12.2':
    resolution: {integrity: sha512-BpcOjWCJub6nRZUS2zA20pmLvjtqAtGejETaIyRLiZiQf++cbrjltLA5NN/xaXfqeOBOSlMFbemIl5/S5tljmg==}
    cpu: [x64]
    os: [freebsd]

  '@unrs/resolver-binding-linux-arm-gnueabihf@1.12.2':
    resolution: {integrity: sha512-vZTDvdSISZjJx66OzJqtsOhzifbqRjbmI1Mnu49fQDwog5GtDI4QidRiEAYbZCRj9C8YZEW+3ZjqsyS9GR4k2A==}
    cpu: [arm]
    os: [linux]

  '@unrs/resolver-binding-linux-arm-musleabihf@1.12.2':
    resolution: {integrity: sha512-BiPI+IrIlwcW4nLLMM21+B1dFPzd55yAVgVGrdgDjNef+ch03GdxrcyaIz8X9SsQirh/kCQ7mviyWlMxdh2D7g==}
    cpu: [arm]
    os: [linux]

  '@unrs/resolver-binding-linux-arm64-gnu@1.12.2':
    resolution: {integrity: sha512-zJc0H99FEPoFfSrNpa91HYfxzfAJCr502oxNK1cfdC9hlaFI43RT+JFCann9JUgZmLzzntChHyn13Sgn9ljHNg==}
    cpu: [arm64]
    os: [linux]

  '@unrs/resolver-binding-linux-arm64-musl@1.12.2':
    resolution: {integrity: sha512-KQ3Lki6l+Pz1k/eBipN41ES+YUK30beLGb9YqcB1O542cyLCNE6GaxrfcY3T6EezmGGk84wb5XyO9loTM9tkcA==}
    cpu: [arm64]
    os: [linux]

  '@unrs/resolver-binding-linux-loong64-gnu@1.12.2':
    resolution: {integrity: sha512-3SJGEh1DborhG6pyxvhPzCT4bbSIVihsvgJc13P1bHG7KLdNDaF9T3gsTwFc7Jw/5Y5/iWOjkEx7Zy0NvCGX3Q==}
    cpu: [loong64]
    os: [linux]

  '@unrs/resolver-binding-linux-loong64-musl@1.12.2':
    resolution: {integrity: sha512-jiuG/Obbel7uw1PwHNFfrkiKhLAF6mnyZ6aWlOAVN9WqKm8v0OFGnciJIHu8+CMvXLQ8AD51LPzAoUfT21D5Ew==}
    cpu: [loong64]
    os: [linux]

  '@unrs/resolver-binding-linux-ppc64-gnu@1.12.2':
    resolution: {integrity: sha512-q7xRvVpmcfeL+LlZg8Pbbo6QaTZwDU5BaGZbwfhkEsXJn3Was8xYfE0RBH266xZt0rM6B7i8xAYIvjthuUIWHg==}
    cpu: [ppc64]
    os: [linux]

  '@unrs/resolver-binding-linux-riscv64-gnu@1.12.2':
    resolution: {integrity: sha512-0CVdx6lcnT3Q9inOH8tsMIOJ6ImndllMjqJHg8RLVdB7Vq4SfkEXl9mCSsVNuNA4MCYycRicCUxPCabVHJRr6A==}
    cpu: [riscv64]
    os: [linux]

  '@unrs/resolver-binding-linux-riscv64-musl@1.12.2':
    resolution: {integrity: sha512-iOwlRo9vnp6R6ohHQS11n0NnfdXx/omhkocmIfaPRpQhKZ+3BDMkkdRVh53qjkFkpPddf+FETA28NwGN7l5l+w==}
    cpu: [riscv64]
    os: [linux]

  '@unrs/resolver-binding-linux-s390x-gnu@1.12.2':
    resolution: {integrity: sha512-HYJtLfXq94q8iZNFT1lknx258wlkkWhZeUXJRqzKBBUJ00CvZ+N33zgbCqimLjsyw5Va6uUxhVa12mI+kaveEw==}
    cpu: [s390x]
    os: [linux]

  '@unrs/resolver-binding-linux-x64-gnu@1.12.2':
    resolution: {integrity: sha512-mPsUhunKKDih5O96Y6enDQyHc1SqBPlY1E/SfMWDM3EdJ95Z9CArPeCVwCCqbP45ljvivdEk8Fxn+SIb1rDAJQ==}
    cpu: [x64]
    os: [linux]

  '@unrs/resolver-binding-linux-x64-musl@1.12.2':
    resolution: {integrity: sha512-azrt6+5ydLd8Vt210AAFis/lZevSfPw93EJRIJG+xPu4WCJ8K0kppCTpMyLPcKT7H15M4Jnt2tMp5bOvCkRC6A==}
    cpu: [x64]
    os: [linux]

  '@unrs/resolver-binding-openharmony-arm64@1.12.2':
    resolution: {integrity: sha512-YZ9hP4O0X9PQb8eO980qmLNGH4zT3I9+SZTdt0Pr0YyuGQhYKoOZkV02VzrzyOZJ5xIJ3UFIenKkUkGg8GjgWQ==}
    cpu: [arm64]
    os: [openharmony]

  '@unrs/resolver-binding-wasm32-wasi@1.12.2':
    resolution: {integrity: sha512-tYFDIkMxSflfEc/h92ZWNsZlHSwgimbNHSO3PL2JWQHfCuC2q316jMyYU9TIWZsFK2bQwyK5VAdYgn8ygPj69A==}
    engines: {node: '>=14.0.0'}
    cpu: [wasm32]

  '@unrs/resolver-binding-win32-arm64-msvc@1.12.2':
    resolution: {integrity: sha512-qzNyg3xL0VPQmCaUh+N5jSitce6k+uCBfMDesWRnlULOZaqUkaJ0ybdT+UqlAWJoQjuqfIU/0Ptx9bteN4D82g==}
    cpu: [arm64]
    os: [win32]

  '@unrs/resolver-binding-win32-ia32-msvc@1.12.2':
    resolution: {integrity: sha512-WD9sY00OfpHVGfsnHZoA8jVT+esS/Bg8z8jzxp5BnDCjjwsuKsPQrzswwpFy4J1AUJbXPRfkpcX0mXrzeXW79g==}
    cpu: [ia32]
    os: [win32]

  '@unrs/resolver-binding-win32-x64-msvc@1.12.2':
    resolution: {integrity: sha512-nAB74NfSNKknqQ1RrYj6uz8FcXEomu/MATJZxh/x+BArzN2U3JbOYC0APYzUIGhVY3m5hRxA8VPNdPBoG8txlA==}
    cpu: [x64]
    os: [win32]

  '@urql/core@5.2.0':
    resolution: {integrity: sha512-/n0ieD0mvvDnVAXEQgX/7qJiVcvYvNkOHeBvkwtylfjydar123caCXcl58PXFY11oU1oquJocVXHxLAbtv4x1A==}

  '@urql/exchange-retry@1.3.2':
    resolution: {integrity: sha512-TQMCz2pFJMfpNxmSfX1VSfTjwUIFx/mL+p1bnfM1xjjdla7Z+KnGMW/EhFbpckp3LyWAH4PgOsMwOMnIN+MBFg==}
    peerDependencies:
      '@urql/core': ^5.0.0

  '@xmldom/xmldom@0.8.13':
    resolution: {integrity: sha512-KRYzxepc14G/CEpEGc3Yn+JKaAeT63smlDr+vjB8jRfgTBBI9wRj/nkQEO+ucV8p8I9bfKLWp37uHgFrbntPvw==}
    engines: {node: '>=10.0.0'}

  '@xmldom/xmldom@0.9.10':
    resolution: {integrity: sha512-A9gOqLdi6cV4ibazAjcQufGj0B1y/vDqYrcuP6d/6x8P27gRS8643Dj9o1dEKtB6O7fwxb2FgBmJS2mX7gpvdw==}
    engines: {node: '>=14.6'}

  abort-controller@3.0.0:
    resolution: {integrity: sha512-h8lQ8tacZYnR3vNQTgibj+tODHI5/+l06Au2Pcriv/Gmet0eaj4TwWH41sO9wnHDiQsEj19q0drzdWdeAHtweg==}
    engines: {node: '>=6.5'}

  accepts@1.3.8:
    resolution: {integrity: sha512-PYAthTa2m2VKxuvSD3DPC/Gy+U+sOA1LAuT8mkmRuvw+NACSaeXEQ+NHcVF7rONl6qcaxV3Uuemwawk+7+SJLw==}
    engines: {node: '>= 0.6'}

  accepts@2.0.0:
    resolution: {integrity: sha512-5cvg6CtKwfgdmVqY1WIiXKc3Q1bkRqGLi+2W/6ao+6Y7gu/RCwRuAhGEzh5B4KlszSuTLgZYuqFqo5bImjNKng==}
    engines: {node: '>= 0.6'}

  acorn-jsx@5.3.2:
    resolution: {integrity: sha512-rq9s+JNhf0IChjtDXxllJ7g41oZk5SlXtp0LHwyA5cejwn7vKmKp4pPri6YEePv2PU65sAsegbXtIinmDFDXgQ==}
    peerDependencies:
      acorn: ^6.0.0 || ^7.0.0 || ^8.0.0

  acorn@8.16.0:
    resolution: {integrity: sha512-UVJyE9MttOsBQIDKw1skb9nAwQuR5wuGD3+82K6JgJlm/Y+KI92oNsMNGZCYdDsVtRHSak0pcV5Dno5+4jh9sw==}
    engines: {node: '>=0.4.0'}
    hasBin: true

  agent-base@6.0.2:
    resolution: {integrity: sha512-RZNwNclF7+MS/8bDg70amg32dyeZGZxiDuQmZxKLAlQjr3jGyLx+4Kkk58UO7D2QdgFIQCovuSuZESne6RG6XQ==}
    engines: {node: '>= 6.0.0'}

  agent-base@7.1.4:
    resolution: {integrity: sha512-MnA+YT8fwfJPgBx3m60MNqakm30XOkyIoH1y6huTQvC0PwZG7ki8NacLBcrPbNoo8vEZy7Jpuk7+jMO+CUovTQ==}
    engines: {node: '>= 14'}

  ajv@6.15.0:
    resolution: {integrity: sha512-fgFx7Hfoq60ytK2c7DhnF8jIvzYgOMxfugjLOSMHjLIPgenqa7S7oaagATUq99mV6IYvN2tRmC0wnTYX6iPbMw==}

  anser@1.4.10:
    resolution: {integrity: sha512-hCv9AqTQ8ycjpSd3upOJd7vFwW1JaoYQ7tpham03GJ1ca8/65rqn0RpaWpItOAd6ylW9wAw6luXYPJIyPFVOww==}

  ansi-escapes@4.3.2:
    resolution: {integrity: sha512-gKXj5ALrKWQLsYG9jlTRmR/xKluxHV+Z9QEwNIgCfM1/uwPMCuzVVnh5mwTd+OuBZcwSIMbqssNWRm1lE51QaQ==}
    engines: {node: '>=8'}

  ansi-regex@4.1.1:
    resolution: {integrity: sha512-ILlv4k/3f6vfQ4OoP2AGvirOktlQ98ZEL1k9FaQjxa3L1abBgbuTDAdPOpvbGncC0BTVQrl+OM8xZGK6tWXt7g==}
    engines: {node: '>=6'}

  ansi-regex@5.0.1:
    resolution: {integrity: sha512-quJQXlTSUGL2LH9SUXo8VwsY4soanhgo6LNSm84E1LBcE8s3O0wpdiRzyR9z/ZZJMlMWv37qOOb9pdJlMUEKFQ==}
    engines: {node: '>=8'}

  ansi-styles@3.2.1:
    resolution: {integrity: sha512-VT0ZI6kZRdTh8YyJw3SMbYm/u+NqfsAxEpWO0Pf9sq8/e94WxxOpPKx9FR1FlyCtOVDNOQ+8ntlqFxiRc+r5qA==}
    engines: {node: '>=4'}

  ansi-styles@4.3.0:
    resolution: {integrity: sha512-zbB9rCJAT1rbjiVDb2hqKFHNYLxgtk8NURxZ3IZwD3F6NtxbXZQCnnSi1Lkx+IDohdPlFp222wVALIheZJQSEg==}
    engines: {node: '>=8'}

  ansi-styles@5.2.0:
    resolution: {integrity: sha512-Cxwpt2SfTzTtXcfOlzGEee8O+c+MmUgGrNiBcXnuWxuFJHe6a5Hz7qwhwe5OgaSYI0IJvkLqWX1ASG+cJOkEiA==}
    engines: {node: '>=10'}

  any-promise@1.3.0:
    resolution: {integrity: sha512-7UvmKalWRt1wgjL1RrGxoSJW/0QZFIegpeGvZG9kjp8vrRu55XTHbwnqq2GpXm9uLbcuhxm3IqX9OB4MZR1b2A==}

  anymatch@3.1.3:
    resolution: {integrity: sha512-KMReFUr0B4t+D+OBkjR3KYqvocp2XaSzO55UcB6mgQMd3KbcE+mWTyvVV7D/zsdEbNnV6acZUutkiHQXvTr1Rw==}
    engines: {node: '>= 8'}

  arg@5.0.2:
    resolution: {integrity: sha512-PYjyFOLKQ9y57JvQ6QLo8dAgNqswh8M1RMJYdQduT6xbWSgK36P/Z/v+p888pM69jMMfS8Xd8F6I1kQ/I9HUGg==}

  argparse@1.0.10:
    resolution: {integrity: sha512-o5Roy6tNG4SL/FOkCAN6RzjiakZS25RLYFrcMttJqbdd8BWrnA+fGz57iN5Pb06pvBGvl5gQ0B48dJlslXvoTg==}

  argparse@2.0.1:
    resolution: {integrity: sha512-8+9WqebbFzpX9OR+Wa6O29asIogeRMzcGtAINdpMHHyAg10f05aSFVBbcEqGf/PXw1EjAZ+q2/bEBg3DvurK3Q==}

  aria-hidden@1.2.6:
    resolution: {integrity: sha512-ik3ZgC9dY/lYVVM++OISsaYDeg1tb0VtP5uL3ouh1koGOaUMDPpbFIei4JkFimWUFPn90sbMNMXQAIVOlnYKJA==}
    engines: {node: '>=10'}

  aria-query@5.3.0:
    resolution: {integrity: sha512-b0P0sZPKtyu8HkeRAfCq0IfURZK+SuwMjY1UXGBU27wpAiTwQAIlq56IbIO+ytk/JjS1fMR14ee5WBBfKi5J6A==}

  aria-query@5.3.2:
    resolution: {integrity: sha512-COROpnaoap1E2F000S62r6A60uHZnmlvomhfyT2DlTcrY1OrBKn2UhH7qn5wTC9zMvD0AY7csdPSNwKP+7WiQw==}
    engines: {node: '>= 0.4'}

  array-buffer-byte-length@1.0.2:
    resolution: {integrity: sha512-LHE+8BuR7RYGDKvnrmcuSq3tDcKv9OFEXQt/HpbZhY7V6h0zlUXutnAD82GiFx9rdieCMjkvtcsPqBwgUl1Iiw==}
    engines: {node: '>= 0.4'}

  array-includes@3.1.9:
    resolution: {integrity: sha512-FmeCCAenzH0KH381SPT5FZmiA/TmpndpcaShhfgEN9eCVjnFBqq3l1xrI42y8+PPLI6hypzou4GXw00WHmPBLQ==}
    engines: {node: '>= 0.4'}

  array.prototype.findlast@1.2.5:
    resolution: {integrity: sha512-CVvd6FHg1Z3POpBLxO6E6zr+rSKEQ9L6rZHAaY7lLfhKsWYUBBOuMs0e9o24oopj6H+geRCX0YJ+TJLBK2eHyQ==}
    engines: {node: '>= 0.4'}

  array.prototype.findlastindex@1.2.6:
    resolution: {integrity: sha512-F/TKATkzseUExPlfvmwQKGITM3DGTK+vkAsCZoDc5daVygbJBnjEUCbgkAvVFsgfXfX4YIqZ/27G3k3tdXrTxQ==}
    engines: {node: '>= 0.4'}

  array.prototype.flat@1.3.3:
    resolution: {integrity: sha512-rwG/ja1neyLqCuGZ5YYrznA62D4mZXg0i1cIskIUKSiqF3Cje9/wXAls9B9s1Wa2fomMsIv8czB8jZcPmxCXFg==}
    engines: {node: '>= 0.4'}

  array.prototype.flatmap@1.3.3:
    resolution: {integrity: sha512-Y7Wt51eKJSyi80hFrJCePGGNo5ktJCslFuboqJsbf57CCPcm5zztluPlc4/aD8sWsKvlwatezpV4U1efk8kpjg==}
    engines: {node: '>= 0.4'}

  array.prototype.tosorted@1.1.4:
    resolution: {integrity: sha512-p6Fx8B7b7ZhL/gmUsAy0D15WhvDccw3mnGNbZpi3pmeJdxtWsj2jEaI4Y6oo3XiHfzuSgPwKc04MYt6KgvC/wA==}
    engines: {node: '>= 0.4'}

  arraybuffer.prototype.slice@1.0.4:
    resolution: {integrity: sha512-BNoCY6SXXPQ7gF2opIP4GBE+Xw7U+pHMYKuzjgCN3GwiaIR09UUeKfheyIry77QtrCBlC0KK0q5/TER/tYh3PQ==}
    engines: {node: '>= 0.4'}

  asap@2.0.6:
    resolution: {integrity: sha512-BSHWgDSAiKs50o2Re8ppvp3seVHXSRM44cdSsT9FfNEUUZLOGWVCsiWaRPWM1Znn+mqZ1OfVZ3z3DWEzSp7hRA==}

  assert@2.1.0:
    resolution: {integrity: sha512-eLHpSK/Y4nhMJ07gDaAzoX/XAKS8PSaojml3M0DM4JpV1LAi5JOJ/p6H/XWrl8L+DzVEvVCW1z3vWAaB9oTsQw==}

  async-function@1.0.0:
    resolution: {integrity: sha512-hsU18Ae8CDTR6Kgu9DYf0EbCr/a5iGL0rytQDobUcdpYOKokk8LEjVphnXkDkgpi0wYVsqrXuP0bZxJaTqdgoA==}
    engines: {node: '>= 0.4'}

  async-limiter@1.0.1:
    resolution: {integrity: sha512-csOlWGAcRFJaI6m+F2WKdnMKr4HhdhFVBk0H/QbJFMCr+uO2kwohwXQPxw/9OCxp05r5ghVBFSyioixx3gfkNQ==}

  asynckit@0.4.0:
    resolution: {integrity: sha512-Oei9OH4tRh0YqU3GxhX79dM/mwVgvbZJaSNaRk+bshkj0S5cfHcgYakreBjrHwatXKbz+IoIdYLxrKim2MjW0Q==}

  available-typed-arrays@1.0.7:
    resolution: {integrity: sha512-wvUjBtSGN7+7SjNpq/9M2Tg350UZD3q62IFZLbRAR1bSMlCo1ZaeW+BJ+D090e4hIIZLBcTDWe4Mh4jvUDajzQ==}
    engines: {node: '>= 0.4'}

  axios@1.17.0:
    resolution: {integrity: sha512-J8SwNxprqqpbfenehxWYXE7CW+wM1BB4w3+N+g+/Wx40xM4rsLrfPmHHxSWIxJLYDgSY/HqlFPIYb2/S3rxafw==}

  babel-jest@29.7.0:
    resolution: {integrity: sha512-BrvGY3xZSwEcCzKvKsCi2GgHqDqsYkOP4/by5xCgIwGXQxIEh+8ew3gmrE1y7XRR6LHZIj6yLYnUi/mm2KXKBg==}
    engines: {node: ^14.15.0 || ^16.10.0 || >=18.0.0}
    peerDependencies:
      '@babel/core': ^7.8.0

  babel-plugin-istanbul@6.1.1:
    resolution: {integrity: sha512-Y1IQok9821cC9onCx5otgFfRm7Lm+I+wwxOx738M/WLPZ9Q42m4IG5W0FNX8WLL2gYMZo3JkuXIH2DOpWM+qwA==}
    engines: {node: '>=8'}

  babel-plugin-jest-hoist@29.6.3:
    resolution: {integrity: sha512-ESAc/RJvGTFEzRwOTT4+lNDk/GNHMkKbNzsvT0qKRfDyyYTskxB5rnU2njIDYVxXCBHHEI1c0YwHob3WaYujOg==}
    engines: {node: ^14.15.0 || ^16.10.0 || >=18.0.0}

  babel-plugin-polyfill-corejs2@0.4.17:
    resolution: {integrity: sha512-aTyf30K/rqAsNwN76zYrdtx8obu0E4KoUME29B1xj+B3WxgvWkp943vYQ+z8Mv3lw9xHXMHpvSPOBxzAkIa94w==}
    peerDependencies:
      '@babel/core': ^7.4.0 || ^8.0.0-0 <8.0.0

  babel-plugin-polyfill-corejs3@0.13.0:
    resolution: {integrity: sha512-U+GNwMdSFgzVmfhNm8GJUX88AadB3uo9KpJqS3FaqNIPKgySuvMb+bHPsOmmuWyIcuqZj/pzt1RUIUZns4y2+A==}
    peerDependencies:
      '@babel/core': ^7.4.0 || ^8.0.0-0 <8.0.0

  babel-plugin-polyfill-regenerator@0.6.8:
    resolution: {integrity: sha512-M762rNHfSF1EV3SLtnCJXFoQbbIIz0OyRwnCmV0KPC7qosSfCO0QLTSuJX3ayAebubhE6oYBAYPrBA5ljowaZg==}
    peerDependencies:
      '@babel/core': ^7.4.0 || ^8.0.0-0 <8.0.0

  babel-plugin-react-compiler@1.0.0:
    resolution: {integrity: sha512-Ixm8tFfoKKIPYdCCKYTsqv+Fd4IJ0DQqMyEimo+pxUOMUR9cVPlwTrFt9Avu+3cb6Zp3mAzl+t1MrG2fxxKsxw==}

  babel-plugin-react-native-web@0.21.2:
    resolution: {integrity: sha512-SPD0J6qjJn8231i0HZhlAGH6NORe+QvRSQM2mwQEzJ2Fb3E4ruWTiiicPlHjmeWShDXLcvoorOCXjeR7k/lyWA==}

  babel-plugin-syntax-hermes-parser@0.29.1:
    resolution: {integrity: sha512-2WFYnoWGdmih1I1J5eIqxATOeycOqRwYxAQBu3cUu/rhwInwHUg7k60AFNbuGjSDL8tje5GDrAnxzRLcu2pYcA==}

  babel-plugin-syntax-hermes-parser@0.33.3:
    resolution: {integrity: sha512-/Z9xYdaJ1lC0pT9do6TqCqhOSLfZ5Ot8D5za1p+feEfWYupCOfGbhhEXN9r2ZgJtDNUNRw/Z+T2CvAGKBqtqWA==}

  babel-plugin-transform-flow-enums@0.0.2:
    resolution: {integrity: sha512-g4aaCrDDOsWjbm0PUUeVnkcVd6AKJsVc/MbnPhEotEpkeJQP6b8nzewohQi7+QS8UyPehOhGWn0nOwjvWpmMvQ==}

  babel-preset-current-node-syntax@1.2.0:
    resolution: {integrity: sha512-E/VlAEzRrsLEb2+dv8yp3bo4scof3l9nR4lrld+Iy5NyVqgVYUJnDAmunkhPMisRI32Qc4iRiz425d8vM++2fg==}
    peerDependencies:
      '@babel/core': ^7.0.0 || ^8.0.0-0

  babel-preset-expo@54.0.11:
    resolution: {integrity: sha512-dEpeFDtYEFzmWtWVwvt7sUCZH0fxXPfbJlgXd7XNZSQDa/Ki/hTOj9exMTzqR2oyPHDNcE9VxYCJ4oS6xw4Pjg==}
    peerDependencies:
      '@babel/runtime': ^7.20.0
      expo: '*'
      react-refresh: '>=0.14.0 <1.0.0'
    peerDependenciesMeta:
      '@babel/runtime':
        optional: true
      expo:
        optional: true

  babel-preset-jest@29.6.3:
    resolution: {integrity: sha512-0B3bhxR6snWXJZtR/RliHTDPRgn1sNHOR0yVtq/IiQFyuOVjFS+wuio/R4gSNkyYmKmJB4wGZv2NZanmKmTnNA==}
    engines: {node: ^14.15.0 || ^16.10.0 || >=18.0.0}
    peerDependencies:
      '@babel/core': ^7.0.0

  badgin@1.2.3:
    resolution: {integrity: sha512-NQGA7LcfCpSzIbGRbkgjgdWkjy7HI+Th5VLxTJfW5EeaAf3fnS+xWQaQOCYiny+q6QSvxqoSO04vCx+4u++EJw==}

  balanced-match@1.0.2:
    resolution: {integrity: sha512-3oSeUO0TMV67hN1AmbXsK4yaqU7tjiHlbxRDZOpH0KW9+CeX4bRAaX0Anxt0tx2MrpRpWwQaPwIlISEJhYU5Pw==}

  balanced-match@4.0.4:
    resolution: {integrity: sha512-BLrgEcRTwX2o6gGxGOCNyMvGSp35YofuYzw9h1IMTRmKqttAZZVU67bdb9Pr2vUHA8+j3i2tJfjO6C6+4myGTA==}
    engines: {node: 18 || 20 || >=22}

  base64-js@1.5.1:
    resolution: {integrity: sha512-AKpaYlHn8t4SVbOHCy+b5+KKgvR4vrsD8vbvrbiQJps7fKDTkjkDry6ji0rUJjC0kzbNePLwzxq8iypo41qeWA==}

  baseline-browser-mapping@2.10.34:
    resolution: {integrity: sha512-IMDedajPifLnHNY0X9n8hKxRTQ6/eTHwr5bDo04WnuqxyKw6LYtQywCuuqPZwhl3aBXMvQpJov42GLCwRRdQzw==}
    engines: {node: '>=6.0.0'}
    hasBin: true

  better-opn@3.0.2:
    resolution: {integrity: sha512-aVNobHnJqLiUelTaHat9DZ1qM2w0C0Eym4LPI/3JxOnSokGVdsl1T1kN7TFvsEAD8G47A6VKQ0TVHqbBnYMJlQ==}
    engines: {node: '>=12.0.0'}

  big-integer@1.6.52:
    resolution: {integrity: sha512-QxD8cf2eVqJOOz63z6JIN9BzvVs/dlySa5HGSBH5xtR8dPteIRQnBxxKqkNTiT6jbDTF6jAfrd4oMcND9RGbQg==}
    engines: {node: '>=0.6'}

  boolbase@1.0.0:
    resolution: {integrity: sha512-JZOSA7Mo9sNGB8+UjSgzdLtokWAky1zbztM3WRLCbZ70/3cTANmQmOdR7y2g+J0e2WXywy1yS468tY+IruqEww==}

  bplist-creator@0.1.0:
    resolution: {integrity: sha512-sXaHZicyEEmY86WyueLTQesbeoH/mquvarJaQNbjuOQO+7gbFcDEWqKmcWA4cOTLzFlfgvkiVxolk1k5bBIpmg==}

  bplist-parser@0.3.1:
    resolution: {integrity: sha512-PyJxiNtA5T2PlLIeBot4lbp7rj4OadzjnMZD/G5zuBNt8ei/yCU7+wW0h2bag9vr8c+/WuRWmSxbqAl9hL1rBA==}
    engines: {node: '>= 5.10.0'}

  bplist-parser@0.3.2:
    resolution: {integrity: sha512-apC2+fspHGI3mMKj+dGevkGo/tCqVB8jMb6i+OX+E29p0Iposz07fABkRIfVUPNd5A5VbuOz1bZbnmkKLYF+wQ==}
    engines: {node: '>= 5.10.0'}

  brace-expansion@1.1.15:
    resolution: {integrity: sha512-EwOCDEex4quD37XhqM3omwtMoJjr//isUZz1JopUNWms+4Z2ViyM/k1YIRePpoVNnQhENnxtFjLaxNHrT7xIUg==}

  brace-expansion@2.1.1:
    resolution: {integrity: sha512-WR1cURNjuvBLMZBMbqM0UoE+WAfdUcEV1ccD8PVBVOI+Z3ND4+SZbN8RsfT2bMuG1qwz5RFvPukSZm5fF2D5eA==}

  brace-expansion@5.0.6:
    resolution: {integrity: sha512-kLpxurY4Z4r9sgMsyG0Z9uzsBlgiU/EFKhj/h91/8yHu0edo7XuixOIH3VcJ8kkxs6/jPzoI6U9Vj3WqbMQ94g==}
    engines: {node: 18 || 20 || >=22}

  braces@3.0.3:
    resolution: {integrity: sha512-yQbXgO/OSZVD2IsiLlro+7Hf6Q18EJrKSEsdoMzKePKXct3gvD8oLcOQdIzGupr5Fj+EDe8gO/lxc1BzfMpxvA==}
    engines: {node: '>=8'}

  browserslist@4.28.2:
    resolution: {integrity: sha512-48xSriZYYg+8qXna9kwqjIVzuQxi+KYWp2+5nCYnYKPTr0LvD89Jqk2Or5ogxz0NUMfIjhh2lIUX/LyX9B4oIg==}
    engines: {node: ^6 || ^7 || ^8 || ^9 || ^10 || ^11 || ^12 || >=13.7}
    hasBin: true

  bser@2.1.1:
    resolution: {integrity: sha512-gQxTNE/GAfIIrmHLUE3oJyp5FO6HRBfhjnw4/wMmA63ZGDJnWBmgY/lyQBpnDUkGmAhbSe39tx2d/iTOAfglwQ==}

  buffer-from@1.1.2:
    resolution: {integrity: sha512-E+XQCRwSbaaiChtv6k6Dwgc+bx+Bs6vuKJHHl5kox/BaKbhiXzqQOwK4cO22yElGp2OCmjwVhT3HmxgyPGnJfQ==}

  buffer@5.7.1:
    resolution: {integrity: sha512-EHcyIPBQ4BSGlvjB16k5KgAJ27CIsHY/2JBmCRReo48y9rQ3MaUzWX3KVlBa4U7MyX02HdVj0K7C3WaB3ju7FQ==}

  bytes@3.1.2:
    resolution: {integrity: sha512-/Nf7TyzTx6S3yRJObOAV7956r8cr2+Oj8AC5dt8wSP3BQAoeX58NoHyCU8P8zGkNXStjTSi6fzO6F0pBdcYbEg==}
    engines: {node: '>= 0.8'}

  call-bind-apply-helpers@1.0.2:
    resolution: {integrity: sha512-Sp1ablJ0ivDkSzjcaJdxEunN5/XvksFJ2sMBFfq6x0ryhQV/2b/KwFe21cMpmHtPOSij8K99/wSfoEuTObmuMQ==}
    engines: {node: '>= 0.4'}

  call-bind@1.0.9:
    resolution: {integrity: sha512-a/hy+pNsFUTR+Iz8TCJvXudKVLAnz/DyeSUo10I5yvFDQJBFU2s9uqQpoSrJlroHUKoKqzg+epxyP9lqFdzfBQ==}
    engines: {node: '>= 0.4'}

  call-bound@1.0.4:
    resolution: {integrity: sha512-+ys997U96po4Kx/ABpBCqhA9EuxJaQWDQg7295H4hBphv3IZg0boBKuwYpt4YXp6MZ5AmZQnU/tyMTlRpaSejg==}
    engines: {node: '>= 0.4'}

  callsites@3.1.0:
    resolution: {integrity: sha512-P8BjAsXvZS+VIDUI11hHCQEv74YT67YUi5JJFNWIqL235sBmjX4+qx9Muvls5ivyNENctx46xQLQ3aTuE7ssaQ==}
    engines: {node: '>=6'}

  camelcase@5.3.1:
    resolution: {integrity: sha512-L28STB170nwWS63UjtlEOE3dldQApaJXZkOI1uMFfzf3rRuPegHaHesyee+YxQ+W6SvRDQV6UrdOdRiR153wJg==}
    engines: {node: '>=6'}

  camelcase@6.3.0:
    resolution: {integrity: sha512-Gmy6FhYlCY7uOElZUSbxo2UCDH8owEk996gkbrpsgGtrJLM3J7jGxl9Ic7Qwwj4ivOE5AWZWRMecDdF7hqGjFA==}
    engines: {node: '>=10'}

  caniuse-lite@1.0.30001797:
    resolution: {integrity: sha512-l8xKG+gwAIExZGl9FrF7KUwuOmk6wbEPC9Xoy/RtnWv1XG0Q4LFlagaLpUv3Kiza3W/wm27zy0yWJEieYKAP6w==}

  chalk@2.4.2:
    resolution: {integrity: sha512-Mti+f9lpJNcwF4tWV8/OrTTtF1gZi+f8FqlyAdouralcFWFQWF2+NgCHShjkCb+IFBLq9buZwE1xckQU4peSuQ==}
    engines: {node: '>=4'}

  chalk@4.1.2:
    resolution: {integrity: sha512-oKnbhFyRIXpUuez8iBMmyEa4nbj4IOQyuhc/wy9kY7/WVPcwIO9VA668Pu8RkO7+0G76SLROeyw9CpQ061i4mA==}
    engines: {node: '>=10'}

  char-regex@1.0.2:
    resolution: {integrity: sha512-kWWXztvZ5SBQV+eRgKFeh8q5sLuZY2+8WUIzlxWVTg+oGwY14qylx1KbKzHd8P6ZYkAg0xyIDU9JMHhyJMZ1jw==}
    engines: {node: '>=10'}

  chownr@3.0.0:
    resolution: {integrity: sha512-+IxzY9BZOQd/XuYPRmrvEVjF/nqj5kgT4kEq7VofrDoM1MxoRjEWkrCC3EtLi59TVawxTAn+orJwFQcrqEN1+g==}
    engines: {node: '>=18'}

  chrome-launcher@0.15.2:
    resolution: {integrity: sha512-zdLEwNo3aUVzIhKhTtXfxhdvZhUghrnmkvcAq2NoDd+LeOHKf03H5jwZ8T/STsAlzyALkBVK552iaG1fGf1xVQ==}
    engines: {node: '>=12.13.0'}
    hasBin: true

  chromium-edge-launcher@0.2.0:
    resolution: {integrity: sha512-JfJjUnq25y9yg4FABRRVPmBGWPZZi+AQXT4mxupb67766/0UlhG8PAZCz6xzEMXTbW3CsSoE8PcCWA49n35mKg==}

  ci-info@2.0.0:
    resolution: {integrity: sha512-5tK7EtrZ0N+OLFMthtqOj4fI2Jeb88C4CAZPu25LDVUgXJ0A3Js4PMGqrn0JU1W0Mh1/Z8wZzYPxqUrXeBboCQ==}

  ci-info@3.9.0:
    resolution: {integrity: sha512-NIxF55hv4nSqQswkAeiOi1r83xy8JldOFDTWiug55KBu9Jnblncd2U6ViHmYgHf01TPZS77NJBhBMKdWj9HQMQ==}
    engines: {node: '>=8'}

  cjs-module-lexer@1.4.3:
    resolution: {integrity: sha512-9z8TZaGM1pfswYeXrUpzPrkx8UnWYdhJclsiYMm6x/w5+nN+8Tf/LnAgfLGQCm59qAOxU8WwHEq2vNwF6i4j+Q==}

  cli-cursor@2.1.0:
    resolution: {integrity: sha512-8lgKz8LmCRYZZQDpRyT2m5rKJ08TnU4tR9FFFW2rxpxR1FzWi4PQ/NfyODchAatHaUgnSPVcx/R5w6NuTBzFiw==}
    engines: {node: '>=4'}

  cli-spinners@2.9.2:
    resolution: {integrity: sha512-ywqV+5MmyL4E7ybXgKys4DugZbX0FC6LnwrhjuykIjnK9k8OQacQ7axGKnjDXWNhns0xot3bZI5h55H8yo9cJg==}
    engines: {node: '>=6'}

  client-only@0.0.1:
    resolution: {integrity: sha512-IV3Ou0jSMzZrd3pZ48nLkT9DA7Ag1pnPzaiQhpW7c3RbcqqzvzzVu+L8gfqMp/8IM2MQtSiqaCxrrcfu8I8rMA==}

  cliui@8.0.1:
    resolution: {integrity: sha512-BSeNnyus75C4//NQ9gQt1/csTXyo/8Sb+afLAkzAptFuMsod9HFokGNudZpi/oQV73hnVK+sR+5PVRMd+Dr7YQ==}
    engines: {node: '>=12'}

  clone@1.0.4:
    resolution: {integrity: sha512-JQHZ2QMW6l3aH/j6xCqQThY/9OH4D/9ls34cgkUBiEeocRTU04tHfKPBsUK1PqZCUQM7GiA0IIXJSuXHI64Kbg==}
    engines: {node: '>=0.8'}

  co@4.6.0:
    resolution: {integrity: sha512-QVb0dM5HvG+uaxitm8wONl7jltx8dqhfU33DcqtOZcLSVIKSDDLDi7+0LbAKiyI8hD9u42m2YxXSkMGWThaecQ==}
    engines: {iojs: '>= 1.0.0', node: '>= 0.12.0'}

  collect-v8-coverage@1.0.3:
    resolution: {integrity: sha512-1L5aqIkwPfiodaMgQunkF1zRhNqifHBmtbbbxcr6yVxxBnliw4TDOW6NxpO8DJLgJ16OT+Y4ztZqP6p/FtXnAw==}

  color-convert@1.9.3:
    resolution: {integrity: sha512-QfAUtd+vFdAtFQcC8CCyYt1fYWxSqAiK2cSD6zDB8N3cpsEBAvRxp9zOGg6G/SHHJYAT88/az/IuDGALsNVbGg==}

  color-convert@2.0.1:
    resolution: {integrity: sha512-RRECPsj7iu/xb5oKYcsFHSppFNnsj/52OVTRKb4zP5onXwVF3zVmmToNcOfGC+CRDpfK/U584fMg38ZHCaElKQ==}
    engines: {node: '>=7.0.0'}

  color-name@1.1.3:
    resolution: {integrity: sha512-72fSenhMw2HZMTVHeCA9KCmpEIbzWiQsjN+BHcBbS9vr1mtt+vJjPdksIBNUmKAW8TFUDPJK5SUU3QhE9NEXDw==}

  color-name@1.1.4:
    resolution: {integrity: sha512-dOy+3AuW3a2wNbZHIuMZpTcgjGuLU/uBL/ubcZF9OXbDo8ff4O8yVp5Bf0efS8uEoYo5q4Fx7dY9OgQGXgAsQA==}

  color-string@1.9.1:
    resolution: {integrity: sha512-shrVawQFojnZv6xM40anx4CkoDP+fZsw/ZerEMsW/pyzsRbElpsL/DBVW7q3ExxwusdNXI3lXpuhEZkzs8p5Eg==}

  color@4.2.3:
    resolution: {integrity: sha512-1rXeuUUiGGrykh+CeBdu5Ie7OJwinCgQY0bc7GCRxy5xVHy+moaqkpL/jqQq0MtQOeYcrqEz4abc5f0KtU7W4A==}
    engines: {node: '>=12.5.0'}

  combined-stream@1.0.8:
    resolution: {integrity: sha512-FQN4MRfuJeHf7cBbBMJFXhKSDq+2kAArBlmRBvcvFE5BB1HZKXtSFASDhdlz9zOYwxh8lDdnvmMOe/+5cdoEdg==}
    engines: {node: '>= 0.8'}

  commander@12.1.0:
    resolution: {integrity: sha512-Vw8qHK3bZM9y/P10u3Vib8o/DdkvA2OtPtZvD871QKjy74Wj1WSKFILMPRPSdUSx5RFK1arlJzEtA4PkFgnbuA==}
    engines: {node: '>=18'}

  commander@2.20.3:
    resolution: {integrity: sha512-GpVkmM8vF2vQUkj2LvZmD35JxeJOLCwJ9cUkugyk2nuhbv3+mJvpLYYt+0+USMxE+oj+ey/lJEnhZw75x/OMcQ==}

  commander@4.1.1:
    resolution: {integrity: sha512-NOKm8xhkzAjzFx8B2v5OAHT+u5pRQc2UCa2Vq9jYL/31o2wi9mxBA7LIFs3sV5VSC49z6pEhfbMULvShKj26WA==}
    engines: {node: '>= 6'}

  commander@7.2.0:
    resolution: {integrity: sha512-QrWXB+ZQSVPmIWIhtEO9H+gwHaMGYiF5ChvoJ+K9ZGHG/sVsa6yiesAD1GC/x46sET00Xlwo1u49RVVVzvcSkw==}
    engines: {node: '>= 10'}

  compressible@2.0.18:
    resolution: {integrity: sha512-AF3r7P5dWxL8MxyITRMlORQNaOA2IkAFaTr4k7BUumjPtRpGDTZpl0Pb1XCO6JeDCBdp126Cgs9sMxqSjgYyRg==}
    engines: {node: '>= 0.6'}

  compression@1.8.1:
    resolution: {integrity: sha512-9mAqGPHLakhCLeNyxPkK4xVo746zQ/czLH1Ky+vkitMnWfWZps8r0qXuwhwizagCRttsL4lfG4pIOvaWLpAP0w==}
    engines: {node: '>= 0.8.0'}

  concat-map@0.0.1:
    resolution: {integrity: sha512-/Srv4dswyQNBfohGpz9o6Yb3Gz3SrUDqBH5rTuhGR7ahtlbYKnVxw2bCFMRljaA7EXHaXZ8wsHdodFvbkhKmqg==}

  connect@3.7.0:
    resolution: {integrity: sha512-ZqRXc+tZukToSNmh5C2iWMSoV3X1YUcPbqEM4DkEG5tNQXrQUZCNVGGv3IuicnkMtPfGf3Xtp8WCXs295iQ1pQ==}
    engines: {node: '>= 0.10.0'}

  convert-source-map@2.0.0:
    resolution: {integrity: sha512-Kvp459HrV2FEJ1CAsi1Ku+MY3kasH19TFykTz2xWmMeq6bk2NU3XXvfJ+Q61m0xktWwt+1HSYf3JZsTms3aRJg==}

  core-js-compat@3.49.0:
    resolution: {integrity: sha512-VQXt1jr9cBz03b331DFDCCP90b3fanciLkgiOoy8SBHy06gNf+vQ1A3WFLqG7I8TipYIKeYK9wxd0tUrvHcOZA==}

  create-jest@29.7.0:
    resolution: {integrity: sha512-Adz2bdH0Vq3F53KEMJOoftQFutWCukm6J24wbPWRO4k1kMY7gS7ds/uoJkNuV8wDCtWWnuwGcJwpWcih+zEW1Q==}
    engines: {node: ^14.15.0 || ^16.10.0 || >=18.0.0}
    hasBin: true

  cross-fetch@3.2.0:
    resolution: {integrity: sha512-Q+xVJLoGOeIMXZmbUK4HYk+69cQH6LudR0Vu/pRm2YlU/hDV9CiS0gKUMaWY5f2NeUH9C1nV3bsTlCo0FsTV1Q==}

  cross-spawn@7.0.6:
    resolution: {integrity: sha512-uV2QOWP2nWzsy2aMp8aRibhi9dlzF5Hgh5SHaB9OiTGEyDTiJJyx0uy51QXdyWbtAHNua4XJzUKca3OzKUd3vA==}
    engines: {node: '>= 8'}

  crypto-js@4.2.0:
    resolution: {integrity: sha512-KALDyEYgpY+Rlob/iriUtjV6d5Eq+Y191A5g4UqLAi8CyGP9N1+FdVbkc1SxKc2r4YAYqG8JzO2KGL+AizD70Q==}

  css-in-js-utils@3.1.0:
    resolution: {integrity: sha512-fJAcud6B3rRu+KHYk+Bwf+WFL2MDCJJ1XG9x137tJQ0xYxor7XziQtuGFbWNdqrvF4Tk26O3H73nfVqXt/fW1A==}

  css-select@5.2.2:
    resolution: {integrity: sha512-TizTzUddG/xYLA3NXodFM0fSbNizXjOKhqiQQwvhlspadZokn1KDy0NZFS0wuEubIYAV5/c1/lAr0TaaFXEXzw==}

  css-tree@1.1.3:
    resolution: {integrity: sha512-tRpdppF7TRazZrjJ6v3stzv93qxRcSsFmW6cX0Zm2NVKpxE1WV1HblnghVv9TreireHkqI/VDEsfolRF1p6y7Q==}
    engines: {node: '>=8.0.0'}

  css-what@6.2.2:
    resolution: {integrity: sha512-u/O3vwbptzhMs3L1fQE82ZSLHQQfto5gyZzwteVIEyeaY5Fc7R4dapF/BvRoSYFeqfBk4m0V1Vafq5Pjv25wvA==}
    engines: {node: '>= 6'}

  css.escape@1.5.1:
    resolution: {integrity: sha512-YUifsXXuknHlUsmlgyY0PKzgPOr7/FjCePfHNt0jxm83wHZi44VDMQ7/fGNkjY3/jV1MC+1CmZbaHzugyeRtpg==}

  csstype@3.2.3:
    resolution: {integrity: sha512-z1HGKcYy2xA8AGQfwrn0PAy+PB7X/GSj3UVJW9qKyn43xWa+gl5nXmU4qqLMRzWVLFC8KusUX8T/0kCiOYpAIQ==}

  data-view-buffer@1.0.2:
    resolution: {integrity: sha512-EmKO5V3OLXh1rtK2wgXRansaK1/mtVdTUEiEI0W8RkvgT05kfxaH29PliLnpLP73yYO6142Q72QNa8Wx/A5CqQ==}
    engines: {node: '>= 0.4'}

  data-view-byte-length@1.0.2:
    resolution: {integrity: sha512-tuhGbE6CfTM9+5ANGf+oQb72Ky/0+s3xKUpHvShfiz2RxMFgFPjsXuRLBVMtvMs15awe45SRb83D6wH4ew6wlQ==}
    engines: {node: '>= 0.4'}

  data-view-byte-offset@1.0.1:
    resolution: {integrity: sha512-BS8PfmtDGnrgYdOonGZQdLZslWIeCGFP9tpan0hi1Co2Zr2NKADsvGYA8XxuG/4UWgJ6Cjtv+YJnB6MM69QGlQ==}
    engines: {node: '>= 0.4'}

  debug@2.6.9:
    resolution: {integrity: sha512-bC7ElrdJaJnPbAP+1EotYvqZsb3ecl5wi6Bfi6BJTUcNowp6cvspg0jXznRTKDjm/E7AdgFBVeAPVMNcKGsHMA==}
    peerDependencies:
      supports-color: '*'
    peerDependenciesMeta:
      supports-color:
        optional: true

  debug@3.2.7:
    resolution: {integrity: sha512-CFjzYYAi4ThfiQvizrFQevTTXHtnCqWfe7x1AhgEscTz6ZbLbfoLRLPugTQyBth6f8ZERVUSyWHFD/7Wu4t1XQ==}
    peerDependencies:
      supports-color: '*'
    peerDependenciesMeta:
      supports-color:
        optional: true

  debug@4.4.3:
    resolution: {integrity: sha512-RGwwWnwQvkVfavKVt22FGLw+xYSdzARwm0ru6DhTVA3umU5hZc28V3kO4stgYryrTlLpuvgI9GiijltAjNbcqA==}
    engines: {node: '>=6.0'}
    peerDependencies:
      supports-color: '*'
    peerDependenciesMeta:
      supports-color:
        optional: true

  decode-uri-component@0.2.2:
    resolution: {integrity: sha512-FqUYQ+8o158GyGTrMFJms9qh3CqTKvAqgqsTnkLI8sKu0028orqBhxNMFkFen0zGyg6epACD32pjVk58ngIErQ==}
    engines: {node: '>=0.10'}

  dedent@1.7.2:
    resolution: {integrity: sha512-WzMx3mW98SN+zn3hgemf4OzdmyNhhhKz5Ay0pUfQiMQ3e1g+xmTJWp/pKdwKVXhdSkAEGIIzqeuWrL3mV/AXbA==}
    peerDependencies:
      babel-plugin-macros: ^3.1.0
    peerDependenciesMeta:
      babel-plugin-macros:
        optional: true

  deep-extend@0.6.0:
    resolution: {integrity: sha512-LOHxIOaPYdHlJRtCQfDIVZtfw/ufM8+rVj649RIHzcm/vGwQRXFt6OPqIFWsm2XEMrNIEtWR64sY1LEKD2vAOA==}
    engines: {node: '>=4.0.0'}

  deep-is@0.1.4:
    resolution: {integrity: sha512-oIPzksmTg4/MriiaYGO+okXDT7ztn/w3Eptv/+gSIdMdKsJo0u4CfYNFJPy+4SKMuCqGw2wxnA+URMg3t8a/bQ==}

  deepmerge@4.3.1:
    resolution: {integrity: sha512-3sUqbMEc77XqpdNO7FRyRog+eW3ph+GYCbj+rK+uYyRMuwsVy0rMiVtPn+QJlKFvWP/1PYpapqYn0Me2knFn+A==}
    engines: {node: '>=0.10.0'}

  defaults@1.0.4:
    resolution: {integrity: sha512-eFuaLoy/Rxalv2kr+lqMlUnrDWV+3j4pljOIJgLIhI058IQfWJ7vXhyEIHu+HtC738klGALYxOKDO0bQP3tg8A==}

  define-data-property@1.1.4:
    resolution: {integrity: sha512-rBMvIzlpA8v6E+SJZoo++HAYqsLrkg7MSfIinMPFhmkorw7X+dOXVJQs+QT69zGkzMyfDnIMN2Wid1+NbL3T+A==}
    engines: {node: '>= 0.4'}

  define-lazy-prop@2.0.0:
    resolution: {integrity: sha512-Ds09qNh8yw3khSjiJjiUInaGX9xlqZDY7JVryGxdxV7NPeuqQfplOpQ66yJFZut3jLa5zOwkXw1g9EI2uKh4Og==}
    engines: {node: '>=8'}

  define-properties@1.2.1:
    resolution: {integrity: sha512-8QmQKqEASLd5nx0U1B1okLElbUuuttJ/AnYmRXbbbGDWh6uS208EjD4Xqq/I9wK7u0v6O08XhTWnt5XtEbR6Dg==}
    engines: {node: '>= 0.4'}

  delayed-stream@1.0.0:
    resolution: {integrity: sha512-ZySD7Nf91aLB0RxL4KGrKHBXl7Eds1DAmEdcoVawXnLD7SDhpNgtuII2aAkg7a7QS41jxPSZ17p4VdGnMHk3MQ==}
    engines: {node: '>=0.4.0'}

  depd@2.0.0:
    resolution: {integrity: sha512-g7nH6P6dyDioJogAAGprGpCtVImJhpPk/roCzdb3fIh61/s/nPsfR6onyMwkCAR/OlC3yBC0lESvUoQEAssIrw==}
    engines: {node: '>= 0.8'}

  deploy-box-react-native@file:../../deploy-box-react-native:
    resolution: {directory: ../../deploy-box-react-native, type: directory}
    peerDependencies:
      axios: '>=1.0.0'
      expo-linking: '>=6.0.0'
      expo-router: '>=4.0.0'
      expo-secure-store: '>=14.0.0'
      expo-web-browser: '>=14.0.0'
      react: '>=18.0.0'
      react-native: '>=0.73.0'
      zustand: '>=4.0.0'

  dequal@2.0.3:
    resolution: {integrity: sha512-0je+qPKHEMohvfRTCEo3CrPG6cAzAYgmzKyxRiYSSDkS6eGJdyVJm7WaYA5ECaAD9wLB2T4EEeymA5aFVcYXCA==}
    engines: {node: '>=6'}

  destroy@1.2.0:
    resolution: {integrity: sha512-2sJGJTaXIIaR1w4iJSNoN0hnMY7Gpc/n8D4qSCJw8QqFWXf7cuAgnEHxBpweaVcPevC2l3KpjYCx3NypQQgaJg==}
    engines: {node: '>= 0.8', npm: 1.2.8000 || >= 1.4.16}

  detect-libc@2.1.2:
    resolution: {integrity: sha512-Btj2BOOO83o3WyH59e8MgXsxEQVcarkUOpEYrubB0urwnN10yQ364rsiByU11nZlqWYZm05i/of7io4mzihBtQ==}
    engines: {node: '>=8'}

  detect-newline@3.1.0:
    resolution: {integrity: sha512-TLz+x/vEXm/Y7P7wn1EJFNLxYpUD4TgMosxY6fAVJUnJMbupHBOncxyWUG9OpTaH9EBD7uFI5LfEgmMOc54DsA==}
    engines: {node: '>=8'}

  detect-node-es@1.1.0:
    resolution: {integrity: sha512-ypdmJU/TbBby2Dxibuv7ZLW3Bs1QEmM7nHjEANfohJLvE0XVujisn1qPJcZxg+qDucsr+bP6fLD1rPS3AhJ7EQ==}

  diff-sequences@29.6.3:
    resolution: {integrity: sha512-EjePK1srD3P08o2j4f0ExnylqRs5B9tJjcp9t1krH2qRi8CCdsYfwe9JgSLurFBWwq4uOlipzfk5fHNvwFKr8Q==}
    engines: {node: ^14.15.0 || ^16.10.0 || >=18.0.0}

  doctrine@2.1.0:
    resolution: {integrity: sha512-35mSku4ZXK0vfCuHEDAwt55dg2jNajHZ1odvF+8SSr82EsZY4QmXfuWso8oEd8zRhVObSN18aM0CjSdoBX7zIw==}
    engines: {node: '>=0.10.0'}

  doctrine@3.0.0:
    resolution: {integrity: sha512-yS+Q5i3hBf7GBkd4KG8a7eBNNWNGLTaEwwYWUijIYM7zrlYDM0BFXHjjPWlWZ1Rg7UaddZeIDmi9jF3HmqiQ2w==}
    engines: {node: '>=6.0.0'}

  dom-accessibility-api@0.5.16:
    resolution: {integrity: sha512-X7BJ2yElsnOJ30pZF4uIIDfBEVgF4XEBxL9Bxhy6dnrm5hkzqmsWHGTiHqRiITNhMyFLyAiWndIJP7Z1NTteDg==}

  dom-accessibility-api@0.6.3:
    resolution: {integrity: sha512-7ZgogeTnjuHbo+ct10G9Ffp0mif17idi0IyWNVA/wcwcm7NPOD/WEHVP3n7n3MhXqxoIYm8d6MuZohYWIZ4T3w==}

  dom-serializer@2.0.0:
    resolution: {integrity: sha512-wIkAryiqt/nV5EQKqQpo3SToSOV9J0DnbJqwK7Wv/Trc92zIAYZ4FlMu+JPFW1DfGFt81ZTCGgDEabffXeLyJg==}

  domelementtype@2.3.0:
    resolution: {integrity: sha512-OLETBj6w0OsagBwdXnPdN0cnMfF9opN69co+7ZrbfPGrdpPVNBUj02spi6B1N7wChLQiPn4CSH/zJvXw56gmHw==}

  domhandler@5.0.3:
    resolution: {integrity: sha512-cgwlv/1iFQiFnU96XXgROh8xTeetsnJiDsTc7TYCLFd9+/WNkIqPTxiM/8pSd8VIrhXGTf1Ny1q1hquVqDJB5w==}
    engines: {node: '>= 4'}

  domutils@3.2.2:
    resolution: {integrity: sha512-6kZKyUajlDuqlHKVX1w7gyslj9MPIXzIFiz/rGu35uC1wMi+kMhQwGhl4lt9unC9Vb9INnY9Z3/ZA3+FhASLaw==}

  dotenv-expand@11.0.7:
    resolution: {integrity: sha512-zIHwmZPRshsCdpMDyVsqGmgyP0yT8GAgXUnkdAoJisxvf33k7yO6OuoKmcTGuXPWSsm8Oh88nZicRLA9Y0rUeA==}
    engines: {node: '>=12'}

  dotenv@16.4.7:
    resolution: {integrity: sha512-47qPchRCykZC03FhkYAhrvwU4xDBFIj1QPqaarj6mdM/hgUzfPHcpkHJOn3mJAufFeeAxAzeGsr5X0M4k6fLZQ==}
    engines: {node: '>=12'}

  dotenv@16.6.1:
    resolution: {integrity: sha512-uBq4egWHTcTt33a72vpSG0z3HnPuIl6NqYcTrKEg2azoEyl2hpW0zqlxysq2pK9HlDIHyHyakeYaYnSAwd8bow==}
    engines: {node: '>=12'}

  dunder-proto@1.0.1:
    resolution: {integrity: sha512-KIN/nDJBQRcXw0MLVhZE9iQHmG68qAVIBg9CqmUYjmQIhgij9U5MFvrqkUL5FbtyyzZuOeOt0zdeRe4UY7ct+A==}
    engines: {node: '>= 0.4'}

  ee-first@1.1.1:
    resolution: {integrity: sha512-WMwm9LhRUo+WUaRN+vRuETqG89IgZphVSNkdFgeb6sS/E4OrDIN7t48CAewSHXc6C8lefD8KKfr5vY61brQlow==}

  electron-to-chromium@1.5.368:
    resolution: {integrity: sha512-7RckJJK4uESJF9PxvfMWd3TGqIiieUTG4HxnKaKuIpGbcr+r2ZEB3g2gAhCP3Fqm42vJSzLfgab9eva/C4/XVw==}

  emittery@0.13.1:
    resolution: {integrity: sha512-DeWwawk6r5yR9jFgnDKYt4sLS0LmHJJi3ZOnb5/JdbYwj3nW+FxQnHIjhBKz8YLC7oRNPVM9NQ47I3CVx34eqQ==}
    engines: {node: '>=12'}

  emoji-regex@8.0.0:
    resolution: {integrity: sha512-MSjYzcWNOA0ewAHpz0MxpYFvwg6yjy1NG3xteoqz644VCo/RPgnr1/GGt+ic3iJTzQ8Eu3TdM14SawnVUmGE6A==}

  encodeurl@1.0.2:
    resolution: {integrity: sha512-TPJXq8JqFaVYm2CWmPvnP2Iyo4ZSM7/QKcSmuMLDObfpH5fi7RUGmd/rTDf+rut/saiDiQEeVTNgAmJEdAOx0w==}
    engines: {node: '>= 0.8'}

  encodeurl@2.0.0:
    resolution: {integrity: sha512-Q0n9HRi4m6JuGIV1eFlmvJB7ZEVxu93IrMyiMsGC0lrMJMWzRgx6WGquyfQgZVb31vhGgXnfmPNNXmxnOkRBrg==}
    engines: {node: '>= 0.8'}

  entities@4.5.0:
    resolution: {integrity: sha512-V0hjH4dGPh9Ao5p0MoRY6BVqtwCjhz6vI5LT8AJ55H+4g9/4vbHx1I54fS0XuclLhDHArPQCiMjDxjaL8fPxhw==}
    engines: {node: '>=0.12'}

  env-editor@0.4.2:
    resolution: {integrity: sha512-ObFo8v4rQJAE59M69QzwloxPZtd33TpYEIjtKD1rrFDcM1Gd7IkDxEBU+HriziN6HSHQnBJi8Dmy+JWkav5HKA==}
    engines: {node: '>=8'}

  error-ex@1.3.4:
    resolution: {integrity: sha512-sqQamAnR14VgCr1A618A3sGrygcpK+HEbenA/HiEAkkUwcZIIB/tgWqHFxWgOyDh4nB4JCRimh79dR5Ywc9MDQ==}

  error-stack-parser@2.1.4:
    resolution: {integrity: sha512-Sk5V6wVazPhq5MhpO+AUxJn5x7XSXGl1R93Vn7i+zS15KDVxQijejNCrz8340/2bgLBjR9GtEG8ZVKONDjcqGQ==}

  es-abstract@1.24.2:
    resolution: {integrity: sha512-2FpH9Q5i2RRwyEP1AylXe6nYLR5OhaJTZwmlcP0dL/+JCbgg7yyEo/sEK6HeGZRf3dFpWwThaRHVApXSkW3xeg==}
    engines: {node: '>= 0.4'}

  es-define-property@1.0.1:
    resolution: {integrity: sha512-e3nRfgfUZ4rNGL232gUgX06QNyyez04KdjFrF+LTRoOXmrOgFKDg4BCdsjW8EnT69eqdYGmRpJwiPVYNrCaW3g==}
    engines: {node: '>= 0.4'}

  es-errors@1.3.0:
    resolution: {integrity: sha512-Zf5H2Kxt2xjTvbJvP2ZWLEICxA6j+hAmMzIlypy4xcBg1vKVnx89Wy0GbS+kf5cwCVFFzdCFh2XSCFNULS6csw==}
    engines: {node: '>= 0.4'}

  es-iterator-helpers@1.3.2:
    resolution: {integrity: sha512-HVLACW1TppGYjJ8H6/jqH/pqOtKRw6wMlrB23xfExmFWxFquAIWCmwoLsOyN96K4a5KbmOf5At9ZUO3GZbetAw==}
    engines: {node: '>= 0.4'}

  es-object-atoms@1.1.2:
    resolution: {integrity: sha512-HWcBoN6NileqtSydK2FqHbS/LoDd2pqrnQHLyJzBj4kOp/ky2MWMN694xOfkK8/SnUsW2DH7EfyVlydKCsm1Zw==}
    engines: {node: '>= 0.4'}

  es-set-tostringtag@2.1.0:
    resolution: {integrity: sha512-j6vWzfrGVfyXxge+O0x5sh6cvxAog0a/4Rdd2K36zCMV5eJ+/+tOAngRO8cODMNWbVRdVlmGZQL2YS3yR8bIUA==}
    engines: {node: '>= 0.4'}

  es-shim-unscopables@1.1.0:
    resolution: {integrity: sha512-d9T8ucsEhh8Bi1woXCf+TIKDIROLG5WCkxg8geBCbvk22kzwC5G2OnXVMO6FUsvQlgUUXQ2itephWDLqDzbeCw==}
    engines: {node: '>= 0.4'}

  es-to-primitive@1.3.0:
    resolution: {integrity: sha512-w+5mJ3GuFL+NjVtJlvydShqE1eN3h3PbI7/5LAsYJP/2qtuMXjfL2LpHSRqo4b4eSF5K/DH1JXKUAHSB2UW50g==}
    engines: {node: '>= 0.4'}

  escalade@3.2.0:
    resolution: {integrity: sha512-WUj2qlxaQtO4g6Pq5c29GTcWGDyd8itL8zTlipgECz3JesAiiOKotd8JU6otB3PACgG6xkJUyVhboMS+bje/jA==}
    engines: {node: '>=6'}

  escape-html@1.0.3:
    resolution: {integrity: sha512-NiSupZ4OeuGwr68lGIeym/ksIZMJodUGOSCZ/FSnTxcrekbvqrgdUxlJOMpijaKZVjAJrWrGs/6Jy8OMuyj9ow==}

  escape-string-regexp@1.0.5:
    resolution: {integrity: sha512-vbRorB5FUQWvla16U8R/qgaFIya2qGzwDrNmCZuYKrbdSUMG6I1ZCGQRefkRVhuOkIGVne7BQ35DSfo1qvJqFg==}
    engines: {node: '>=0.8.0'}

  escape-string-regexp@2.0.0:
    resolution: {integrity: sha512-UpzcLCXolUWcNu5HtVMHYdXJjArjsF9C0aNnquZYY4uW/Vu0miy5YoWvbV345HauVvcAUnpRuhMMcqTcGOY2+w==}
    engines: {node: '>=8'}

  escape-string-regexp@4.0.0:
    resolution: {integrity: sha512-TtpcNJ3XAzx3Gq8sWRzJaVajRs0uVxA2YAkdb1jm2YkPz4G6egUFAyA3n5vtEIZefPk5Wa4UXbKuS5fKkJWdgA==}
    engines: {node: '>=10'}

  eslint-config-expo@10.0.0:
    resolution: {integrity: sha512-/XC/DvniUWTzU7Ypb/cLDhDD4DXqEio4lug1ObD/oQ9Hcx3OVOR8Mkp4u6U4iGoZSJyIQmIk3WVHe/P1NYUXKw==}
    peerDependencies:
      eslint: '>=8.10'

  eslint-import-resolver-node@0.3.10:
    resolution: {integrity: sha512-tRrKqFyCaKict5hOd244sL6EQFNycnMQnBe+j8uqGNXYzsImGbGUU4ibtoaBmv5FLwJwcFJNeg1GeVjQfbMrDQ==}

  eslint-import-resolver-typescript@3.10.1:
    resolution: {integrity: sha512-A1rHYb06zjMGAxdLSkN2fXPBwuSaQ0iO5M/hdyS0Ajj1VBaRp0sPD3dn1FhME3c/JluGFbwSxyCfqdSbtQLAHQ==}
    engines: {node: ^14.18.0 || >=16.0.0}
    peerDependencies:
      eslint: '*'
      eslint-plugin-import: '*'
      eslint-plugin-import-x: '*'
    peerDependenciesMeta:
      eslint-plugin-import:
        optional: true
      eslint-plugin-import-x:
        optional: true

  eslint-module-utils@2.13.0:
    resolution: {integrity: sha512-bLohSkT6469rRs8czj0tLTD8vaeIS/whvPRJVjDr7IuoTT1k5DYDERlNycjDj/HkOlvQdYurmfZ/g3fG5bgeLQ==}
    engines: {node: '>=4'}
    peerDependencies:
      '@typescript-eslint/parser': '*'
      eslint: '*'
      eslint-import-resolver-node: '*'
      eslint-import-resolver-typescript: '*'
      eslint-import-resolver-webpack: '*'
    peerDependenciesMeta:
      '@typescript-eslint/parser':
        optional: true
      eslint:
        optional: true
      eslint-import-resolver-node:
        optional: true
      eslint-import-resolver-typescript:
        optional: true
      eslint-import-resolver-webpack:
        optional: true

  eslint-plugin-expo@1.0.3:
    resolution: {integrity: sha512-C1v9NPvpDET36+7Klpp/+53Jl+VzOfpbDxpKtL/pAPhCDwTX0kW6Swo425PT0uc4AMT5jpQbB7hSKFjKOGMl4A==}
    engines: {node: '>=18.0.0'}
    peerDependencies:
      eslint: '>=8.10'
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
